5sam/ScanUS/cam_pos.jpg

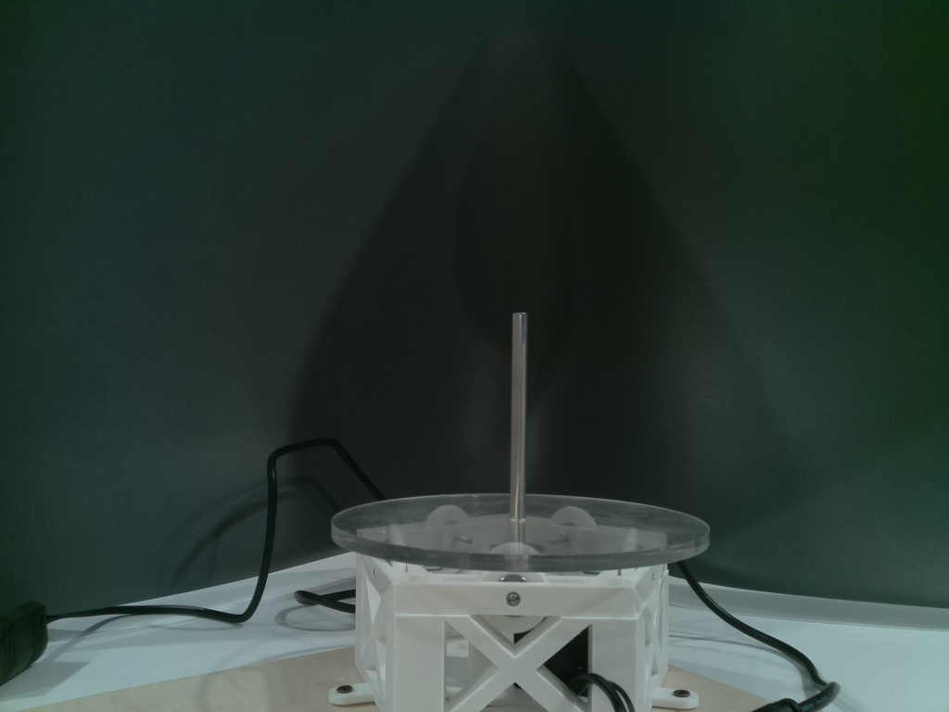
cam_pos.jpg
