5sam/ScanUS/Images/bon_laser_boite.jpg

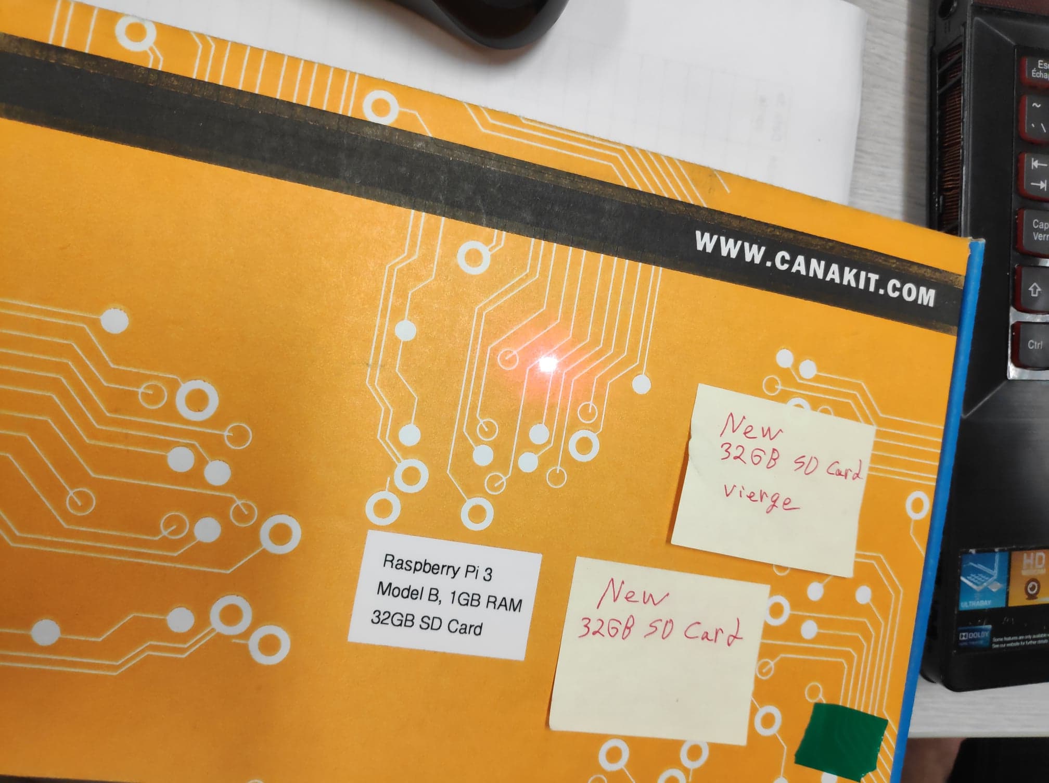
Images/bon_laser_boite.jpg
