5sam/ScanUS/Images/bon_laser_papier.jpg

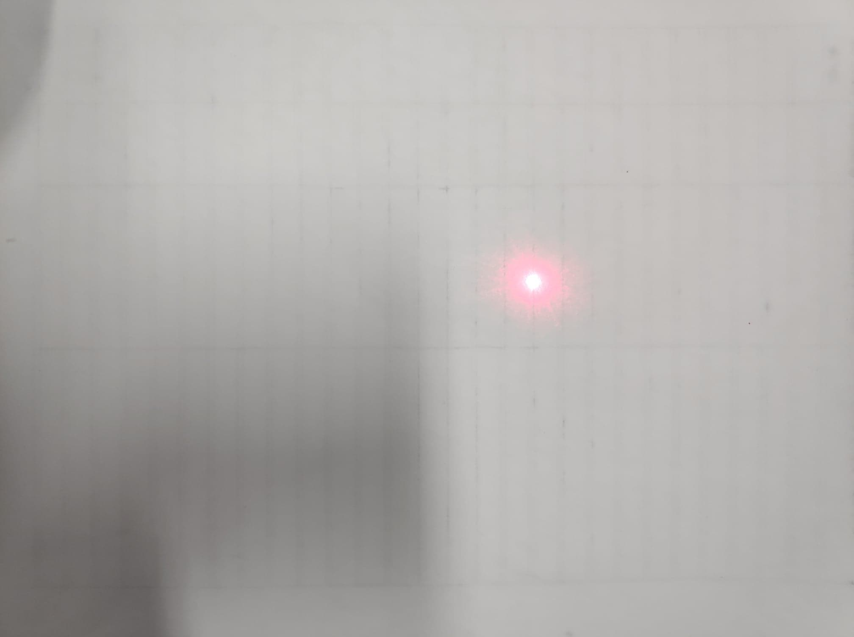
Images/bon_laser_papier.jpg
