5sam/ScanUS/Images/bon_laser_souris_1.jpg

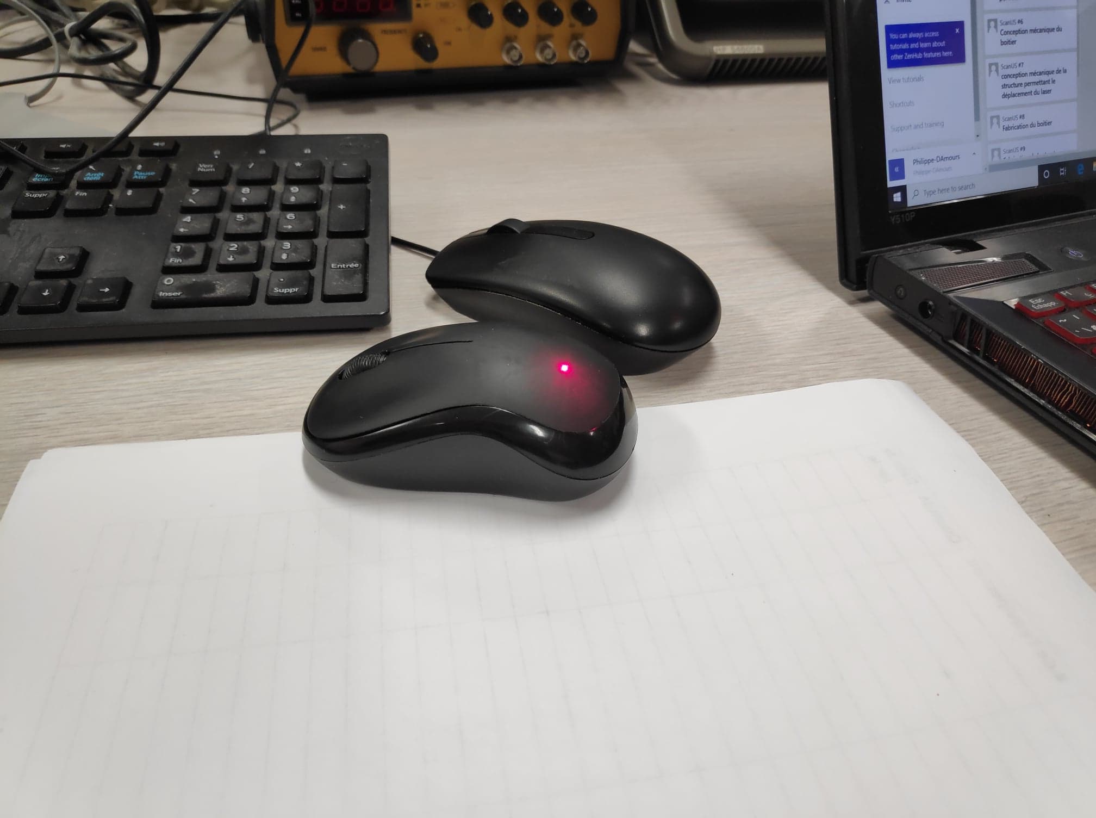
Images/bon_laser_souris_1.jpg
