5sam/ScanUS/Images/bon_laser_souris_2.jpg

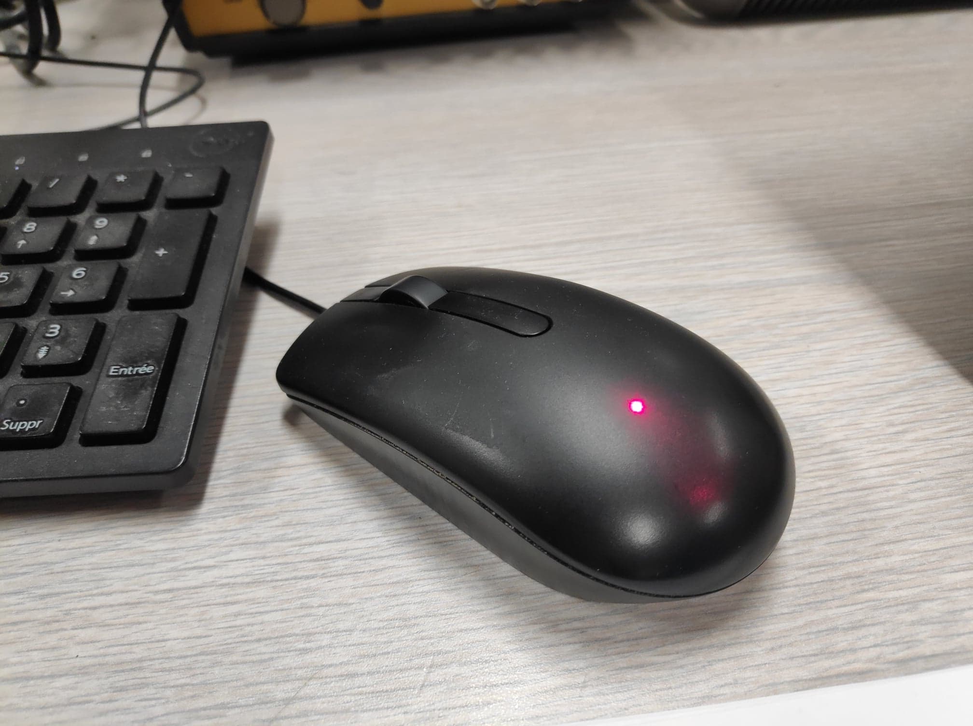
Images/bon_laser_souris_2.jpg
