5sam/ScanUS/Images/red_dot.jpg

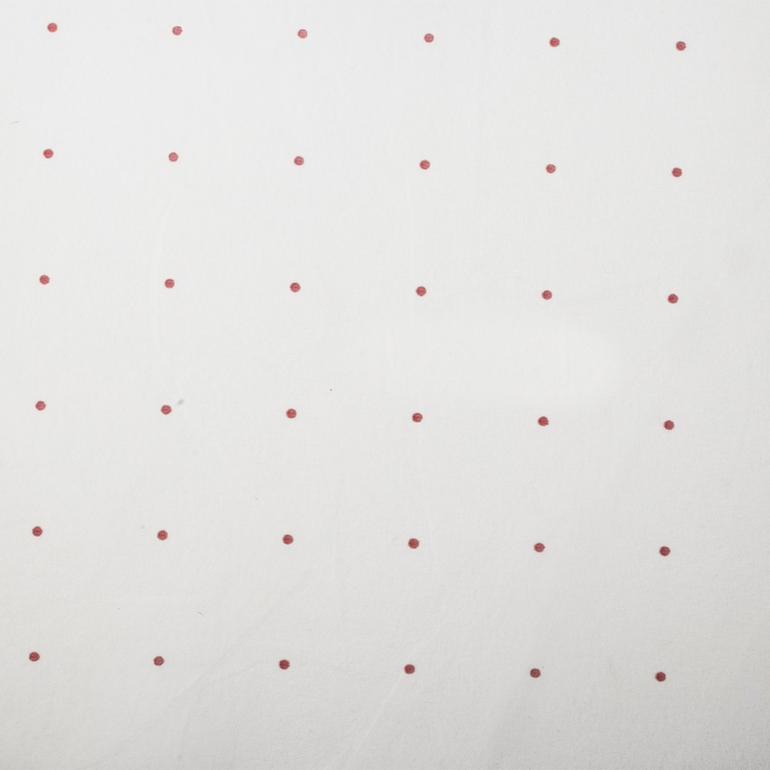
Images/red_dot.jpg
