5sam/ScanUS/imagetestjuan.jpg

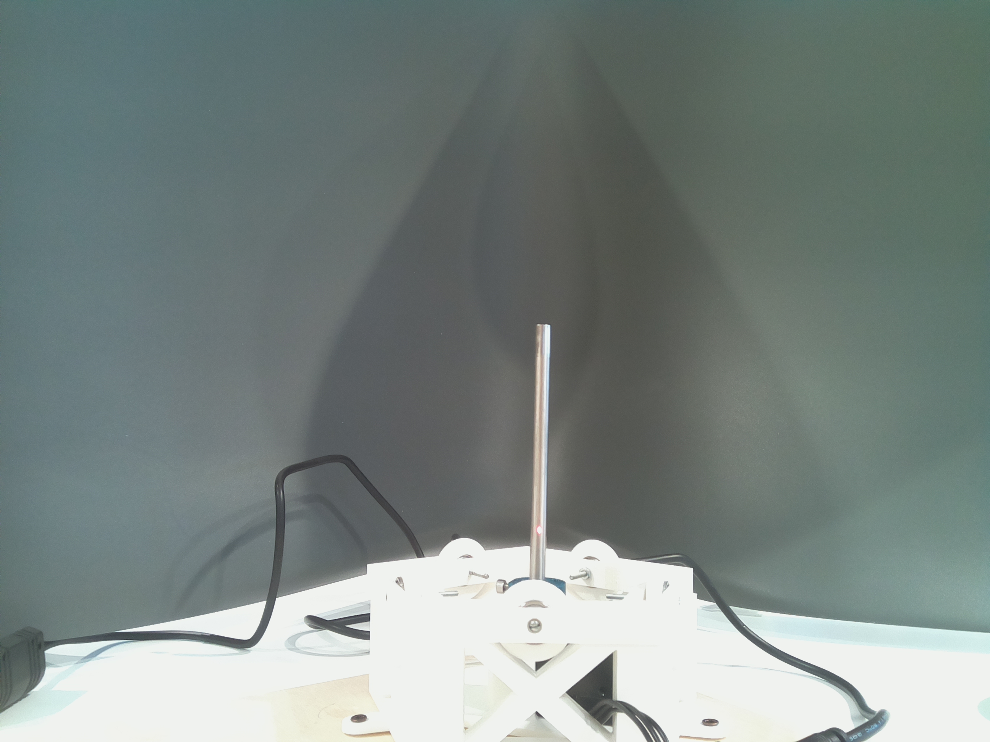
imagetestjuan.jpg
