5sam/ScanUS/Calibration/image_0.png

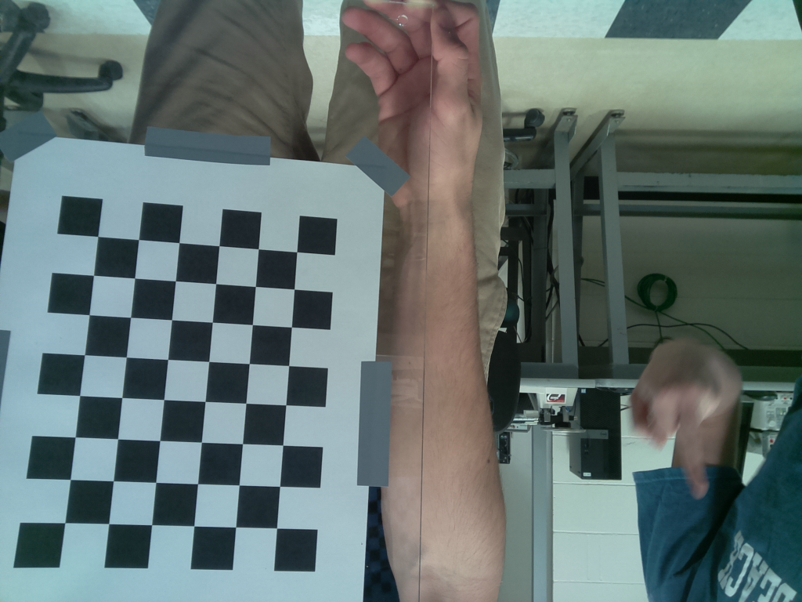
Calibration/image_0.png
