5sam/ScanUS/Calibration/image_1.png

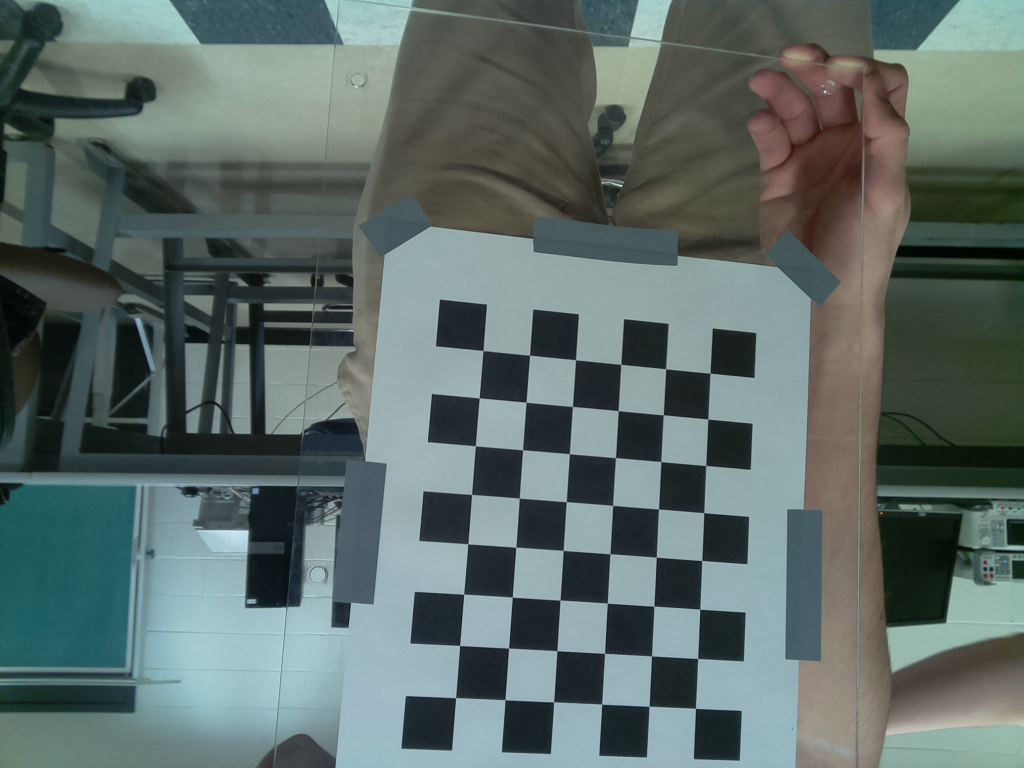
Calibration/image_1.png
