5sam/ScanUS/Calibration/image_2.png

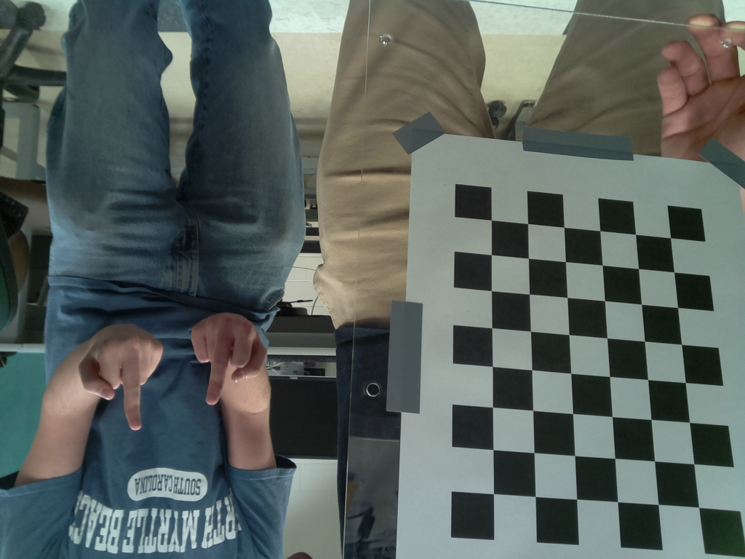
Calibration/image_2.png
