5sam/ScanUS/Calibration/image_3.png

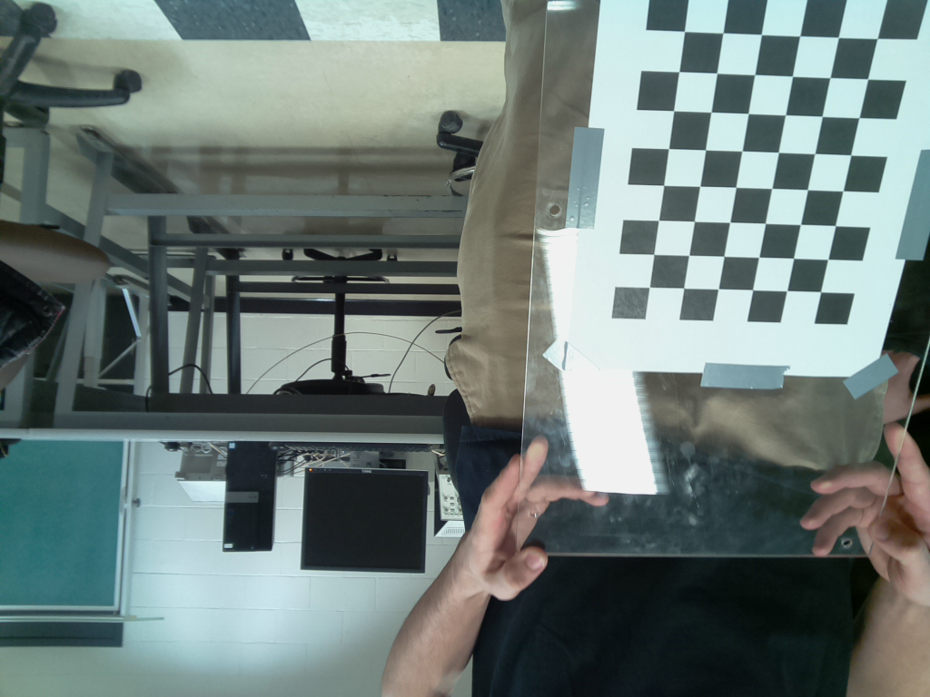
Calibration/image_3.png
