5sam/ScanUS/Calibration/image_4.png

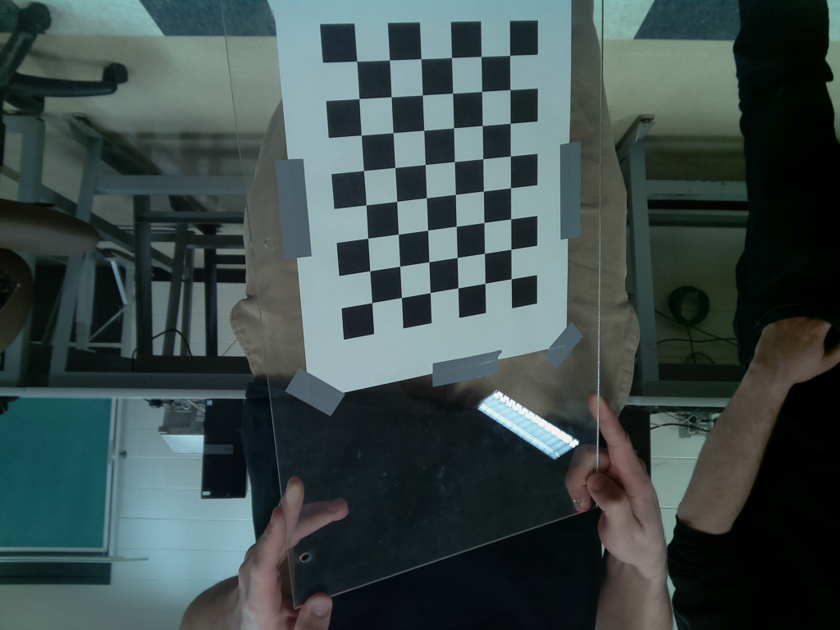
Calibration/image_4.png
