5sam/ScanUS/Calibration/image_5.png

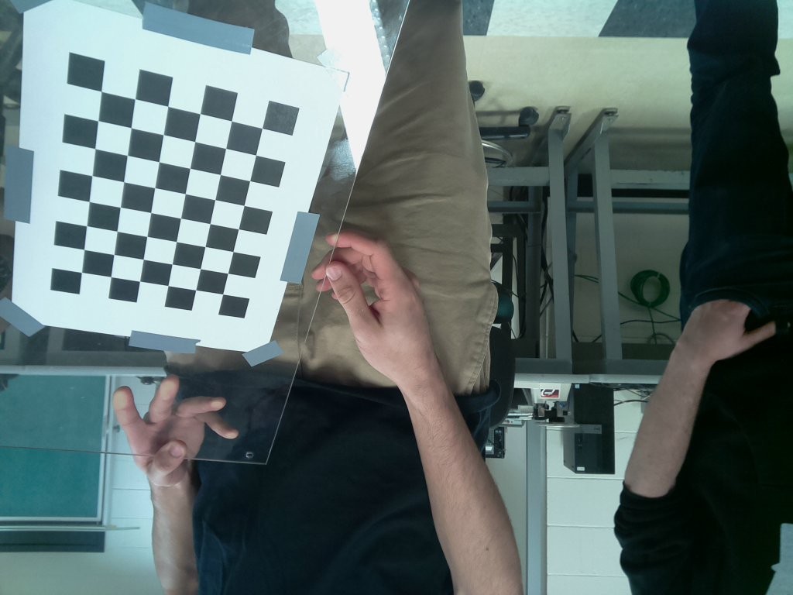
Calibration/image_5.png
