5sam/ScanUS/Calibration/image_6.png

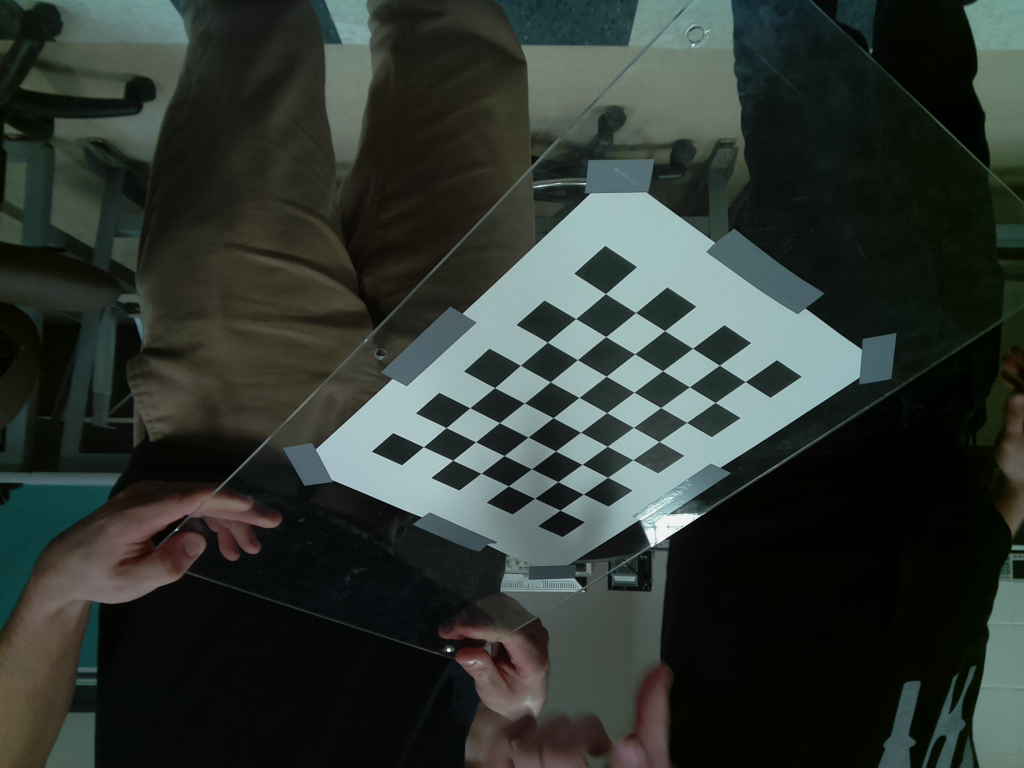
Calibration/image_6.png
