5sam/ScanUS/Calibration/image_7.png

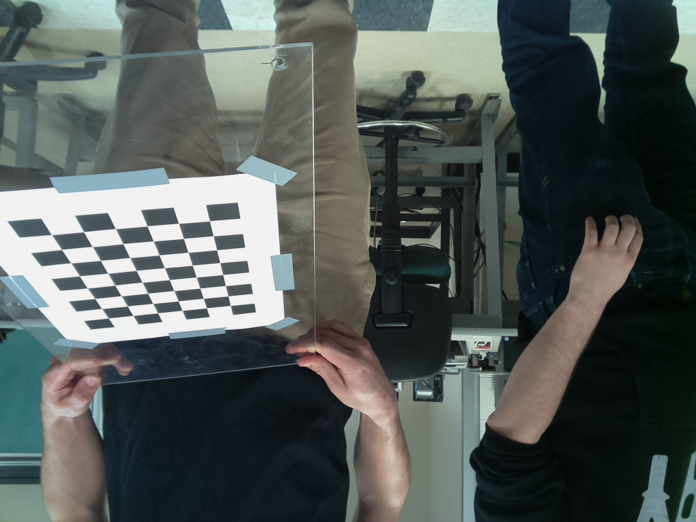
Calibration/image_7.png
