5sam/ScanUS/Calibration/image_8.png

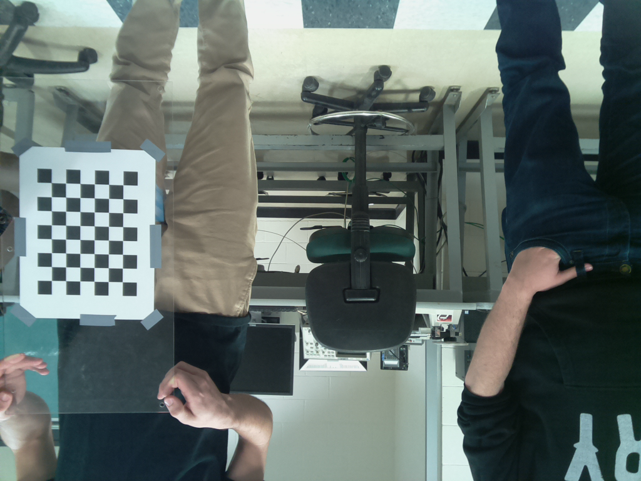
Calibration/image_8.png
