5sam/ScanUS/Calibration/image_9.png

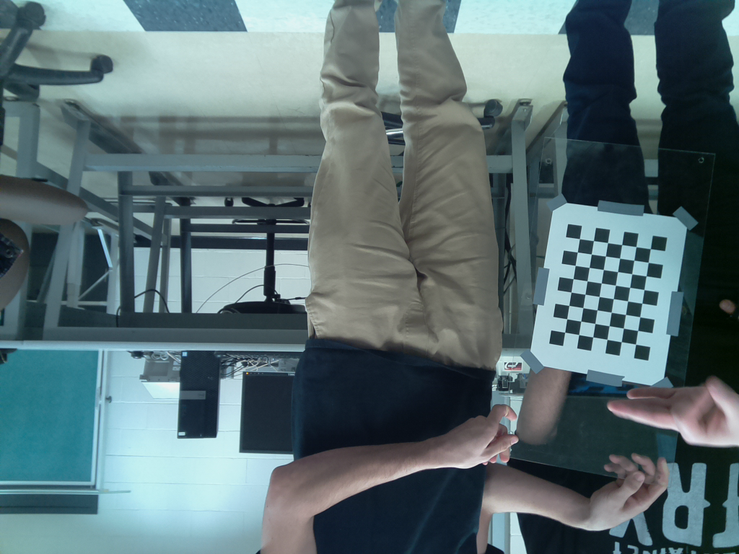
Calibration/image_9.png
