5sam/ScanUS/Calibration/image_11.png

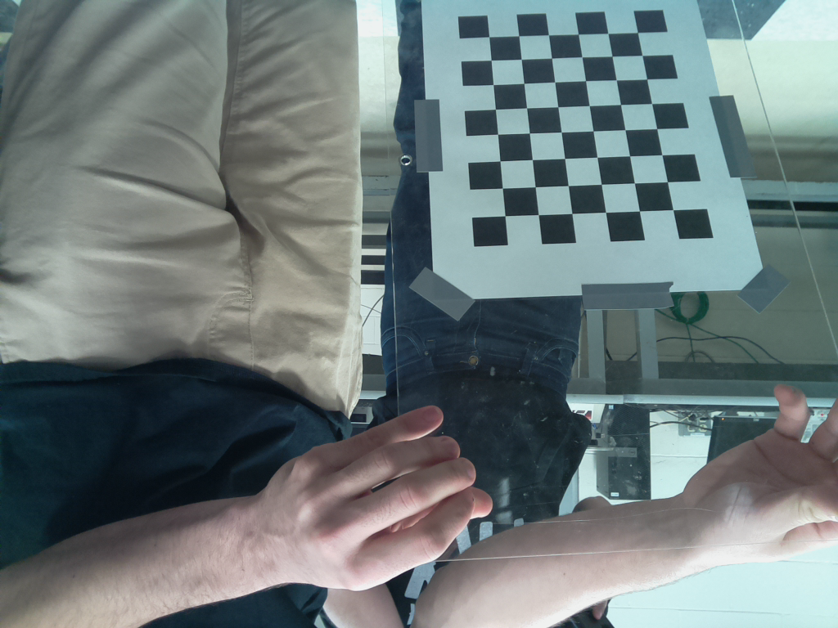
Calibration/image_11.png
