5sam/ScanUS/Calibration/image_12.png

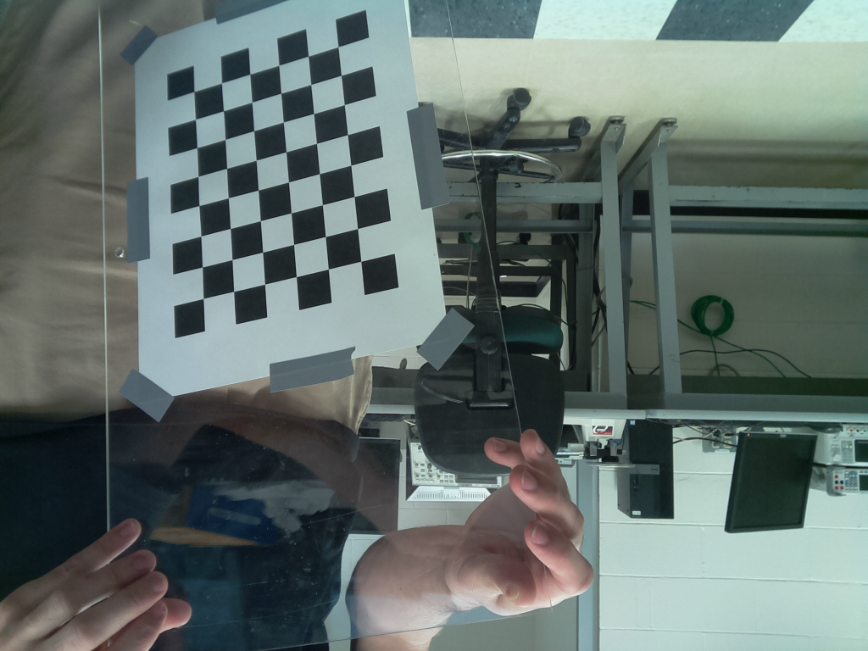
Calibration/image_12.png
