5sam/ScanUS/Calibration/image_13.png

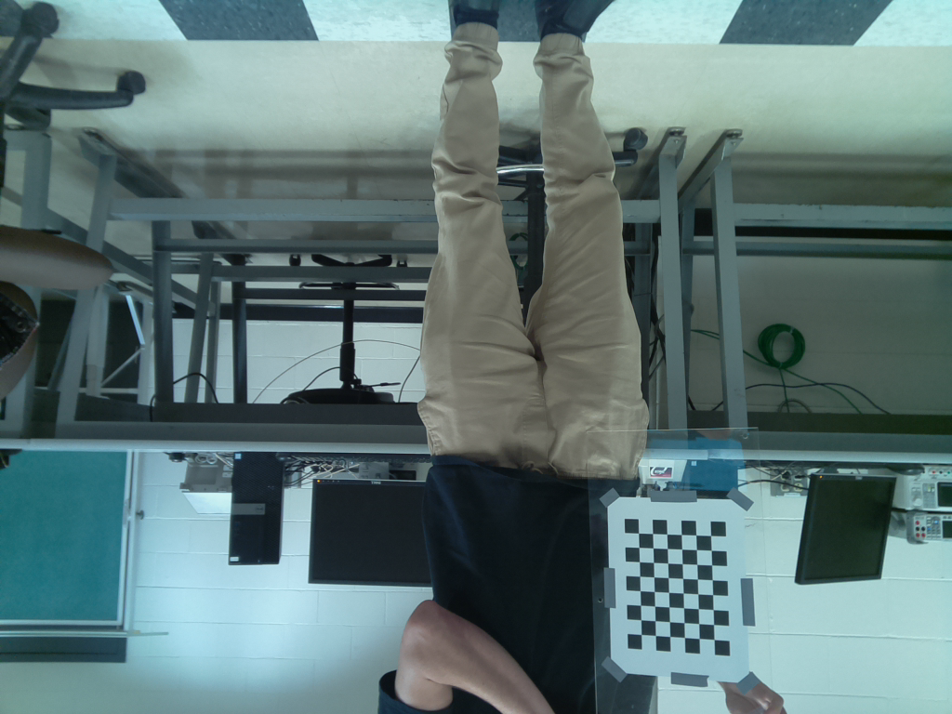
Calibration/image_13.png
