5sam/ScanUS/Calibration/image_14.png

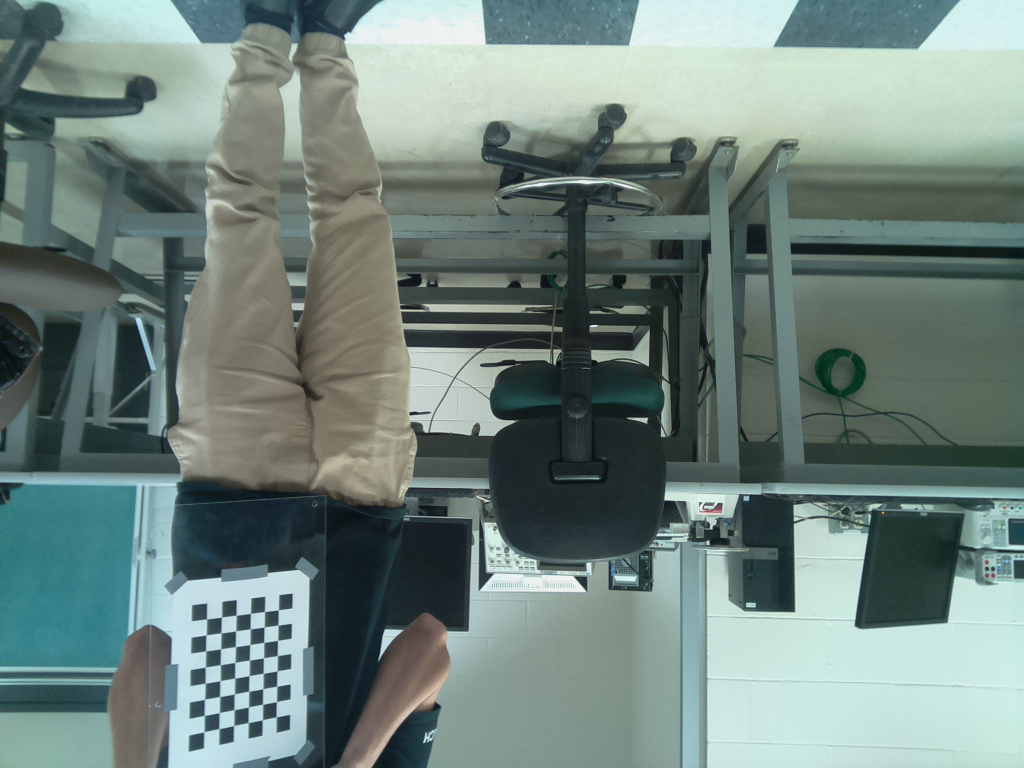
Calibration/image_14.png
