5sam/ScanUS/Calibration/image_15.png

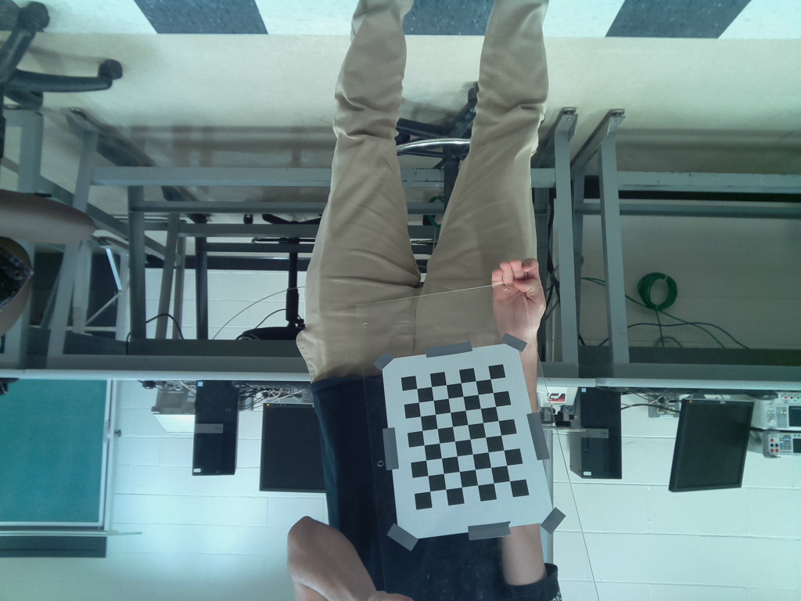
Calibration/image_15.png
