5sam/ScanUS/Calibration/image_16.png

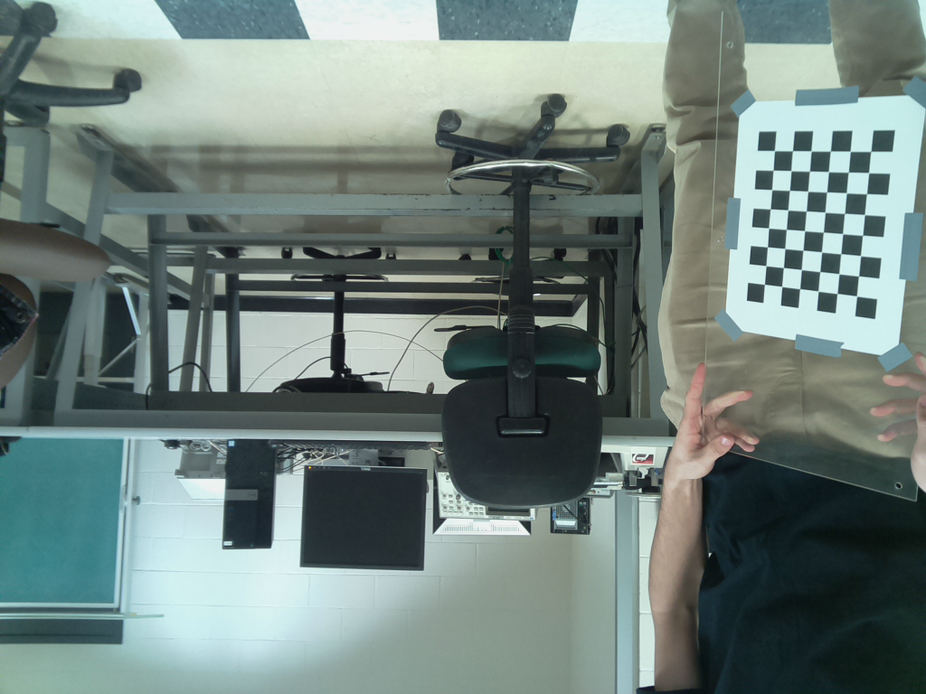
Calibration/image_16.png
