5sam/ScanUS/Calibration/image_17.png

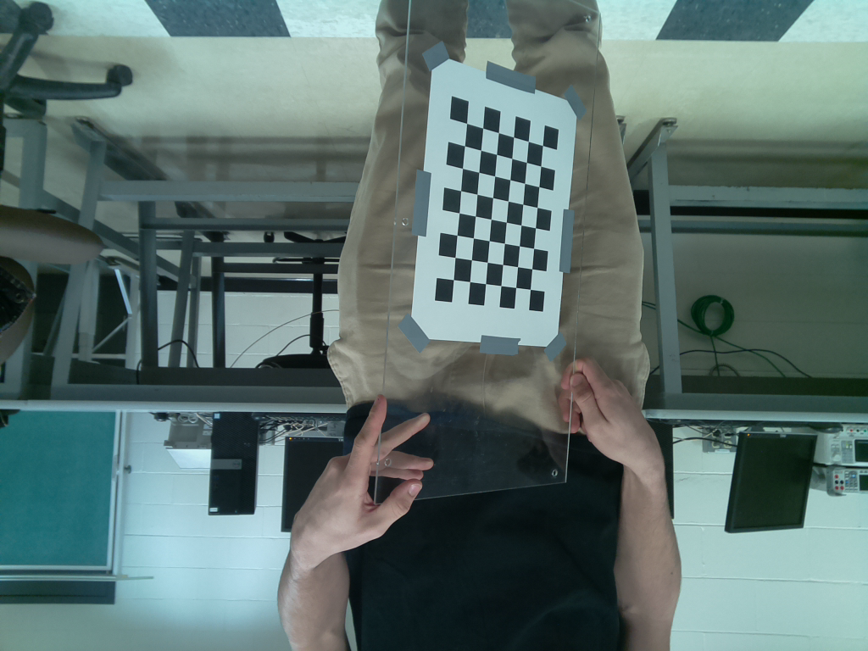
Calibration/image_17.png
