5sam/ScanUS/Calibration/image_19.png

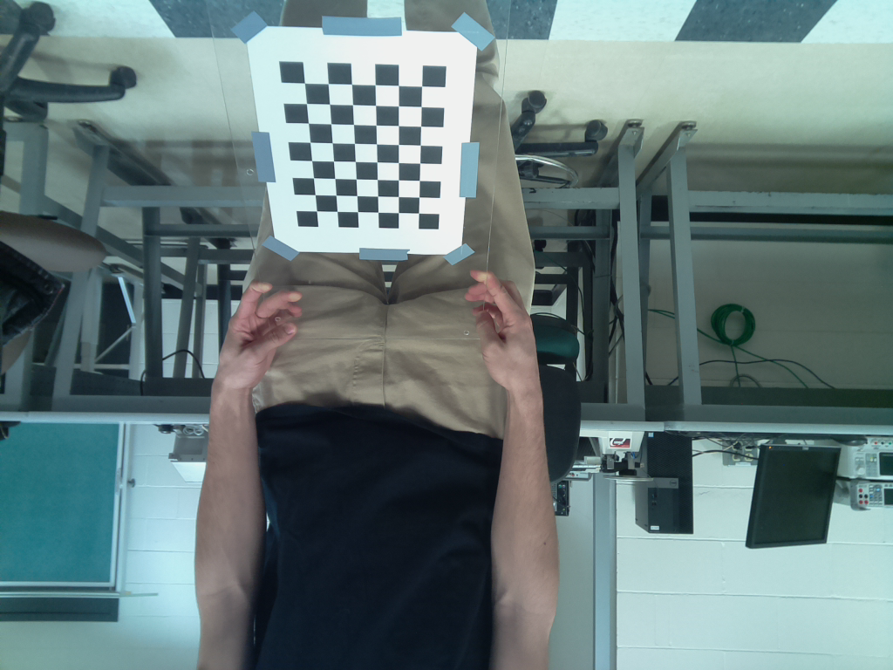
Calibration/image_19.png
