5sam/ScanUS/Calibration/image_20.png

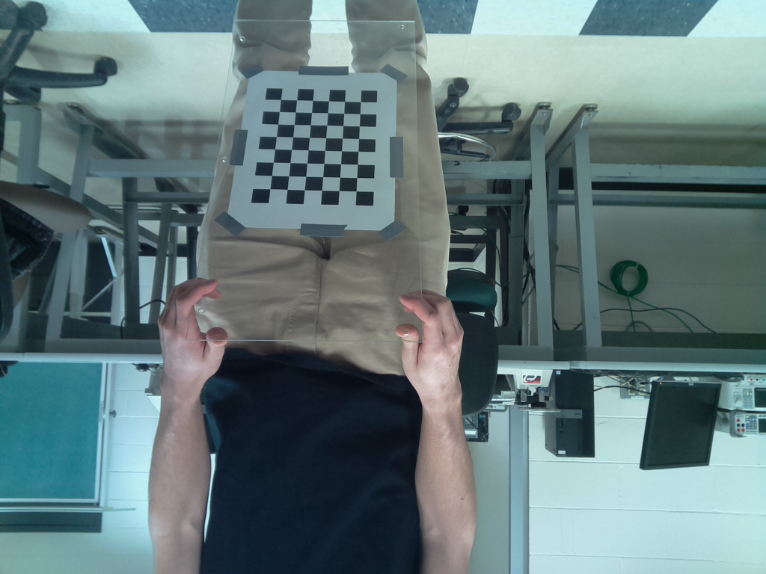
Calibration/image_20.png
