5sam/ScanUS/Calibration/image_21.png

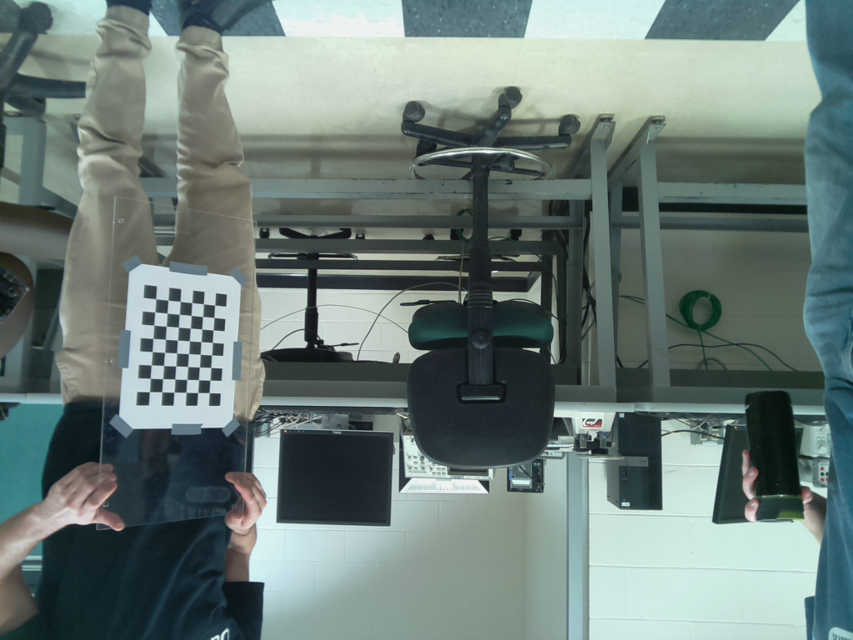
Calibration/image_21.png
