5sam/ScanUS/Calibration/image_23.png

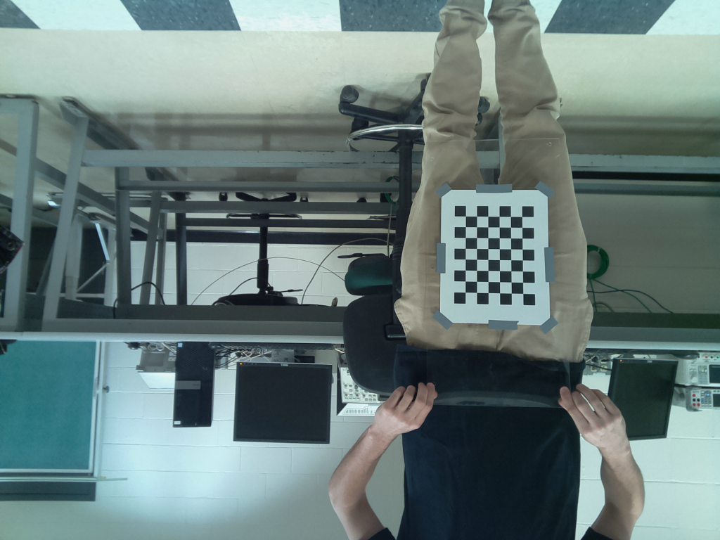
Calibration/image_23.png
