5sam/ScanUS/Calibration/image_24.png

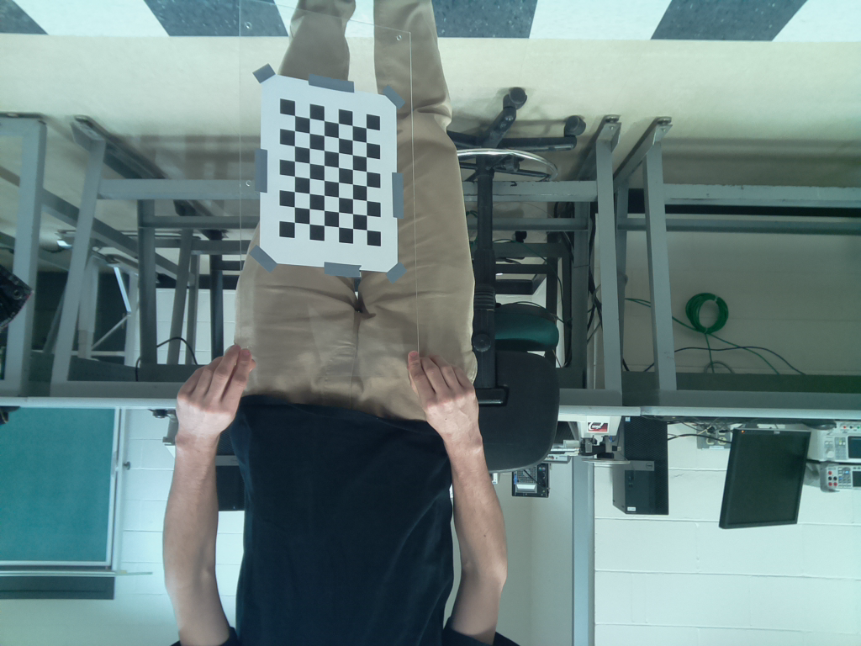
Calibration/image_24.png
