5sam/ScanUS/Calibration/image_25.png

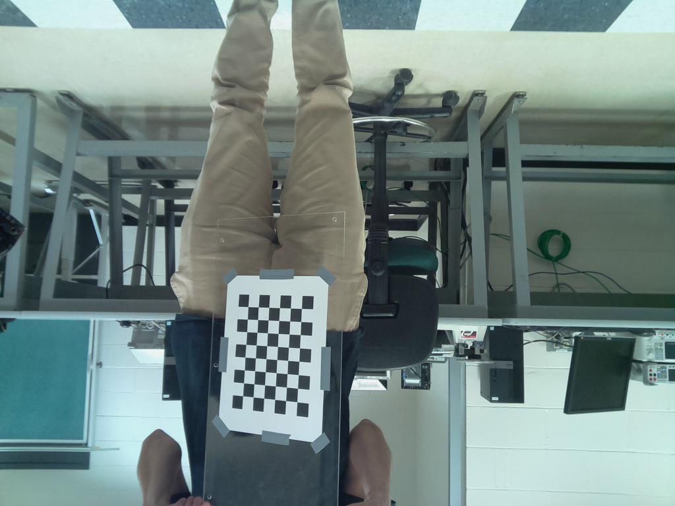
Calibration/image_25.png
