5sam/ScanUS/Calibration/image_26.png

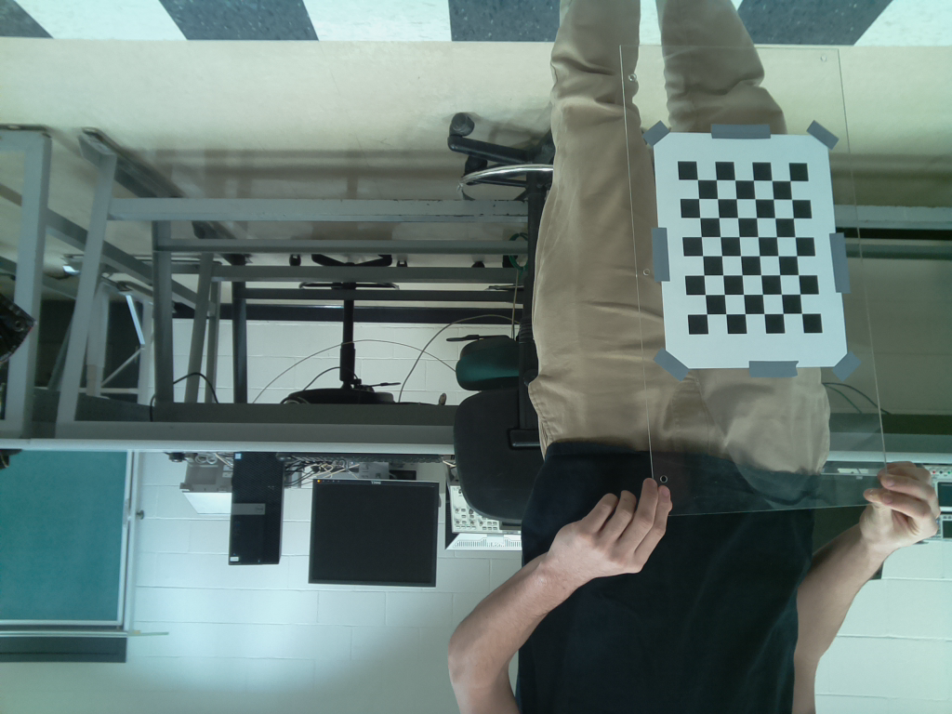
Calibration/image_26.png
