5sam/ScanUS/Calibration/image_27.png

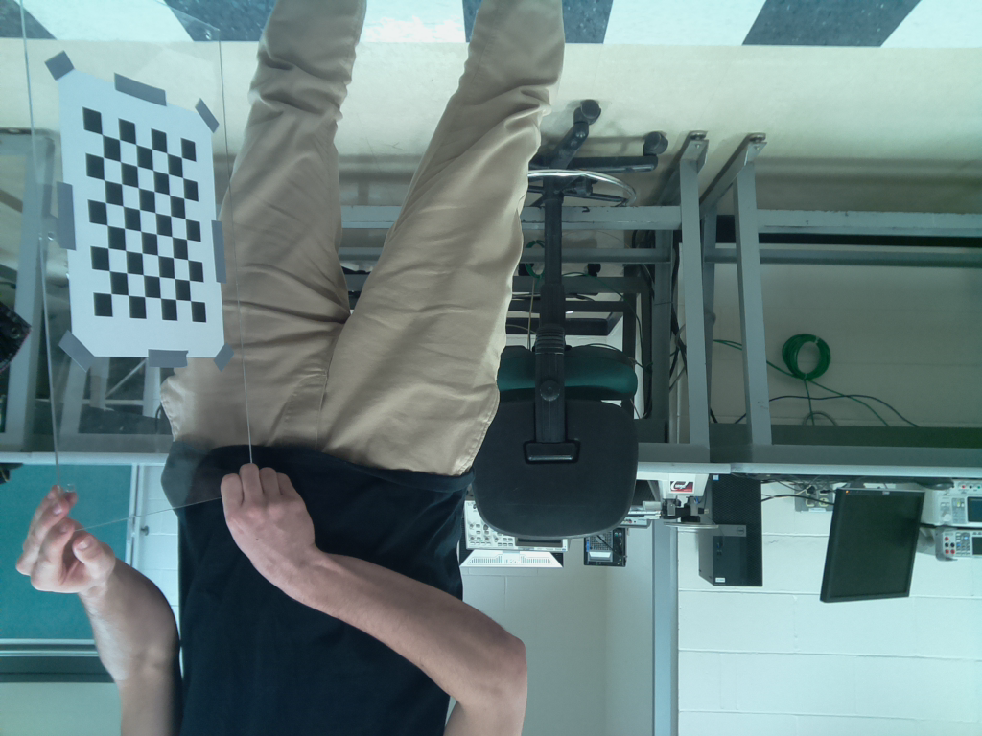
Calibration/image_27.png
