5sam/ScanUS/Calibration/image_28.png

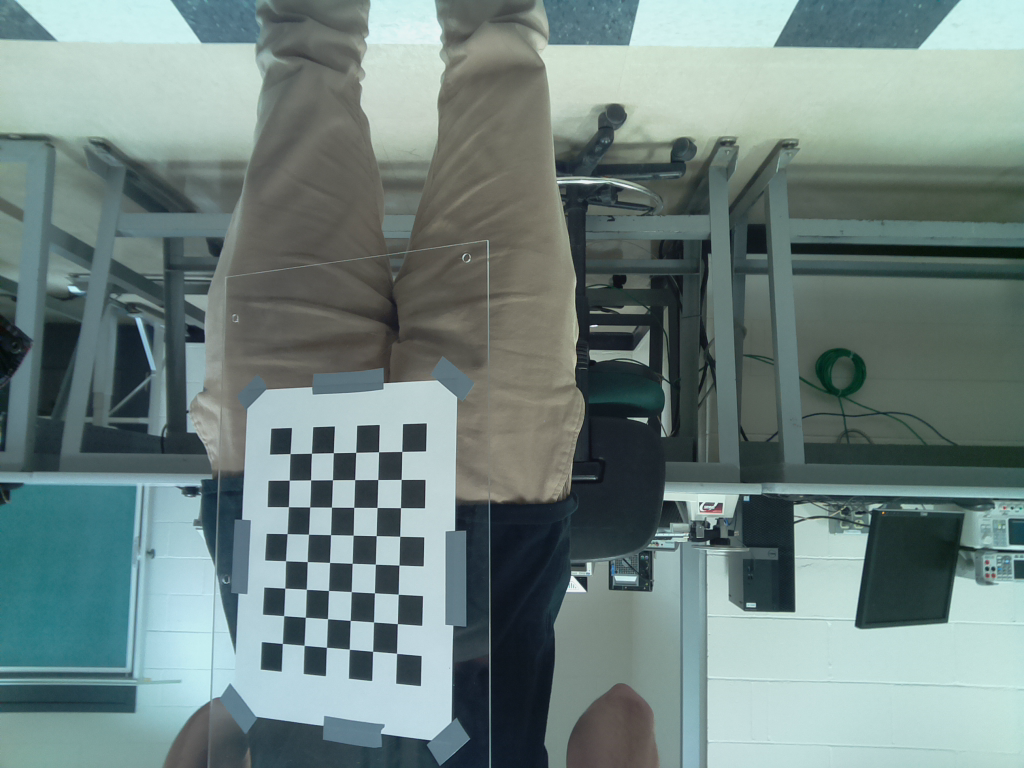
Calibration/image_28.png
