5sam/ScanUS/Calibration/image_29.png

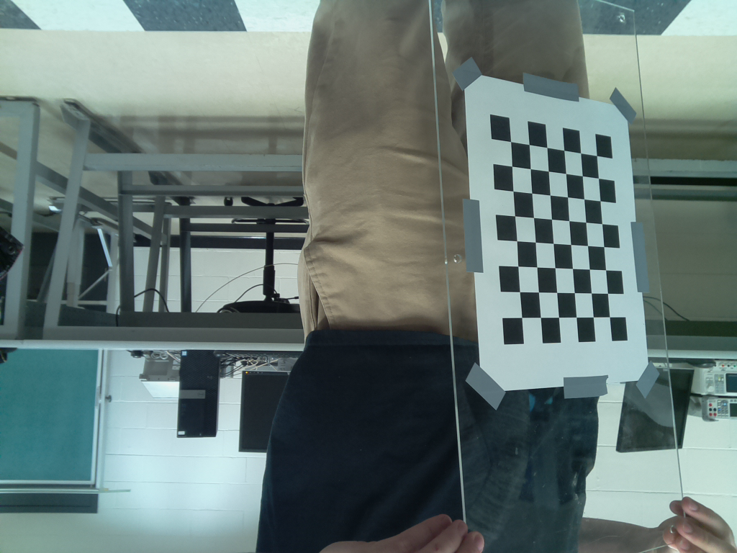
Calibration/image_29.png
