5sam/ScanUS/Calibration/image_30.png

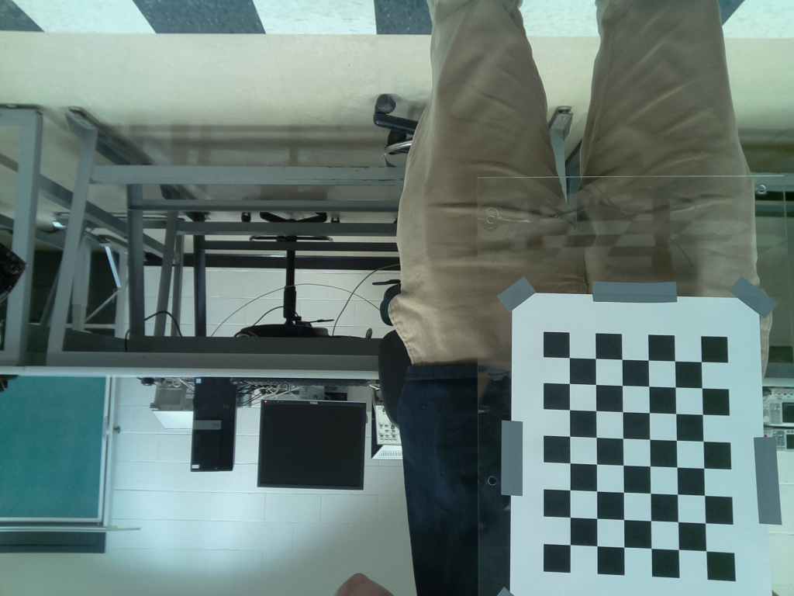
Calibration/image_30.png
