5sam/ScanUS/Calibration/image_31.png

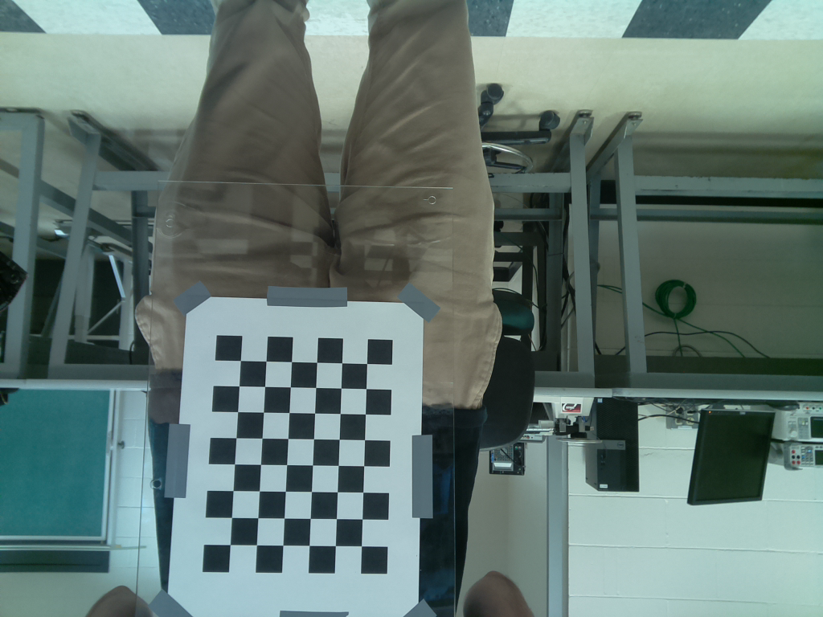
Calibration/image_31.png
