5sam/ScanUS/Calibration/image_32.png

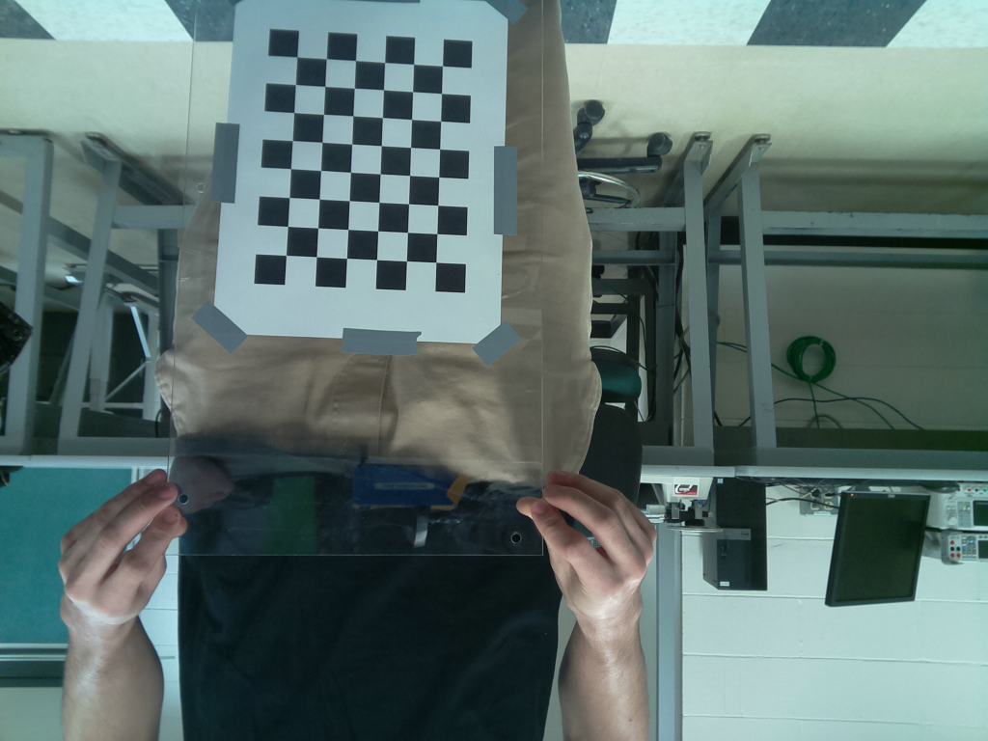
Calibration/image_32.png
