5sam/ScanUS/Calibration/image_33.png

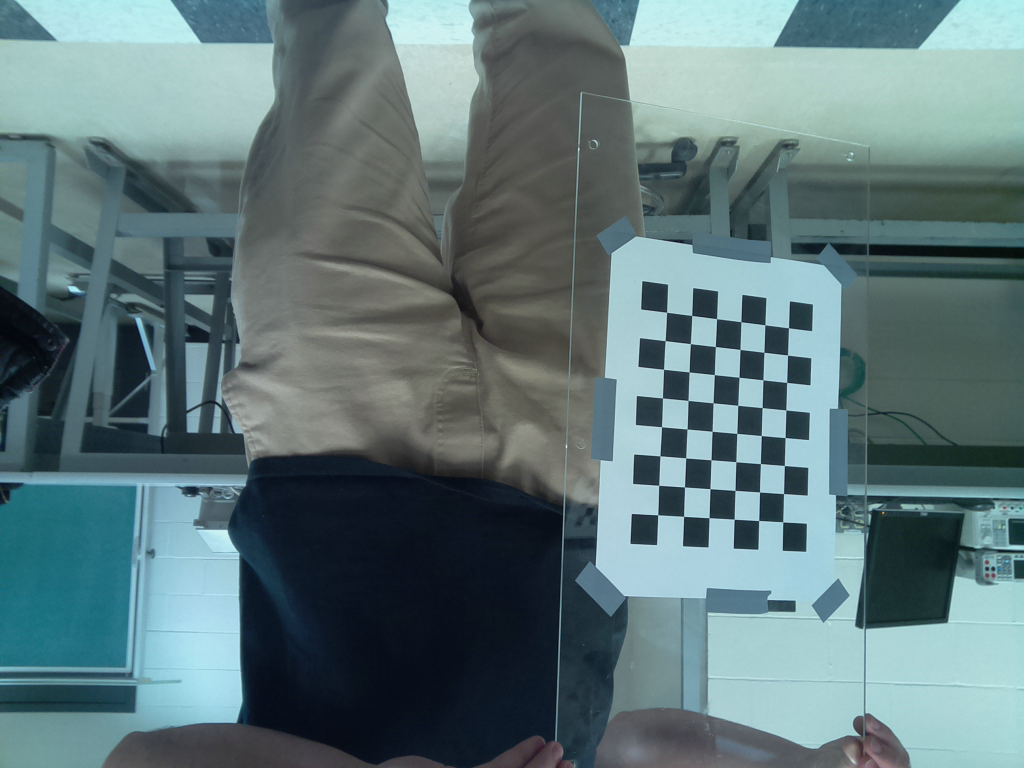
Calibration/image_33.png
