5sam/ScanUS/Calibration/image_34.png

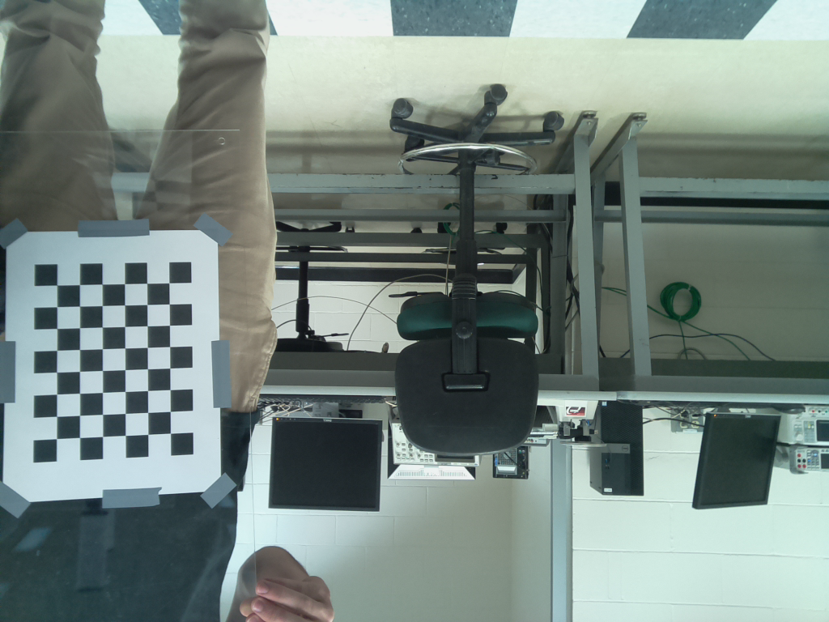
Calibration/image_34.png
