5sam/ScanUS/Calibration/image_35.png

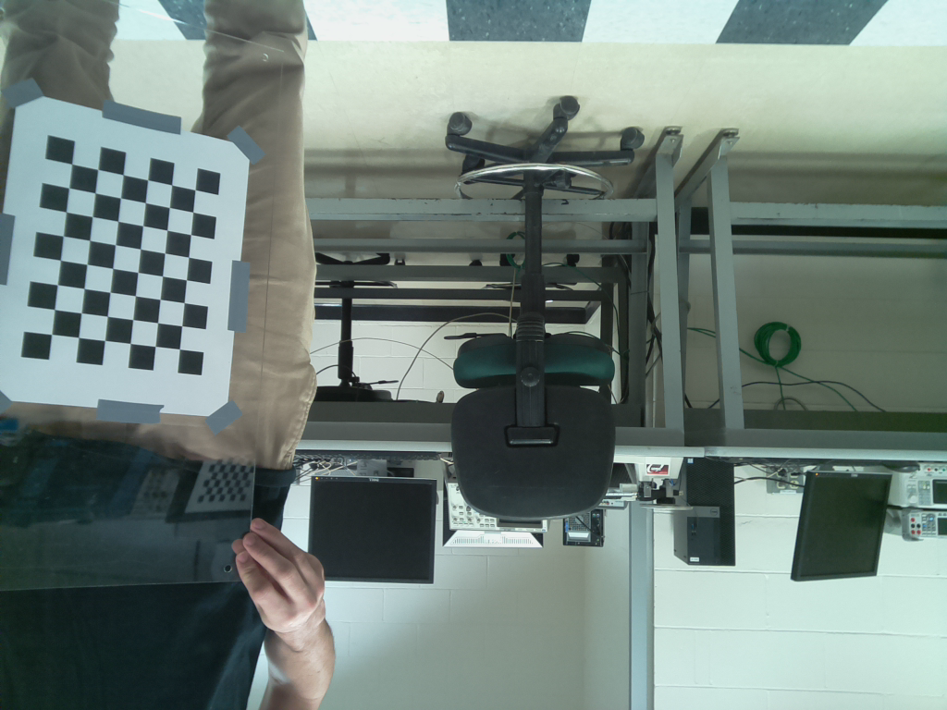
Calibration/image_35.png
