5sam/ScanUS/Calibration/image_36.png

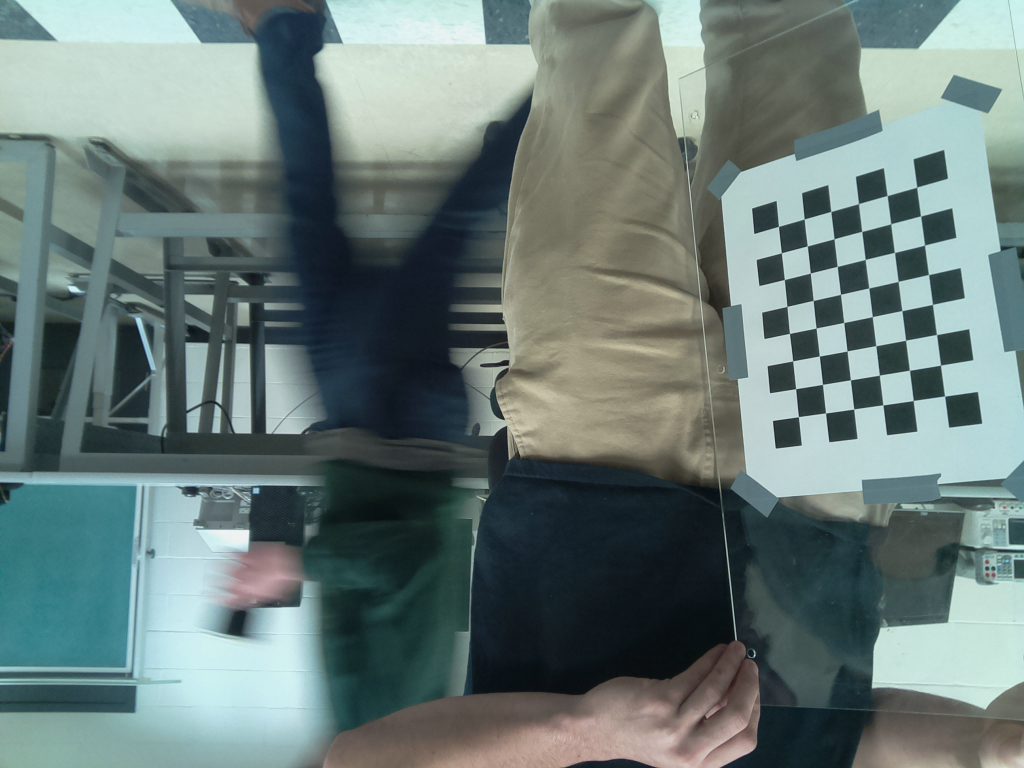
Calibration/image_36.png
