5sam/ScanUS/Calibration/image_39.png

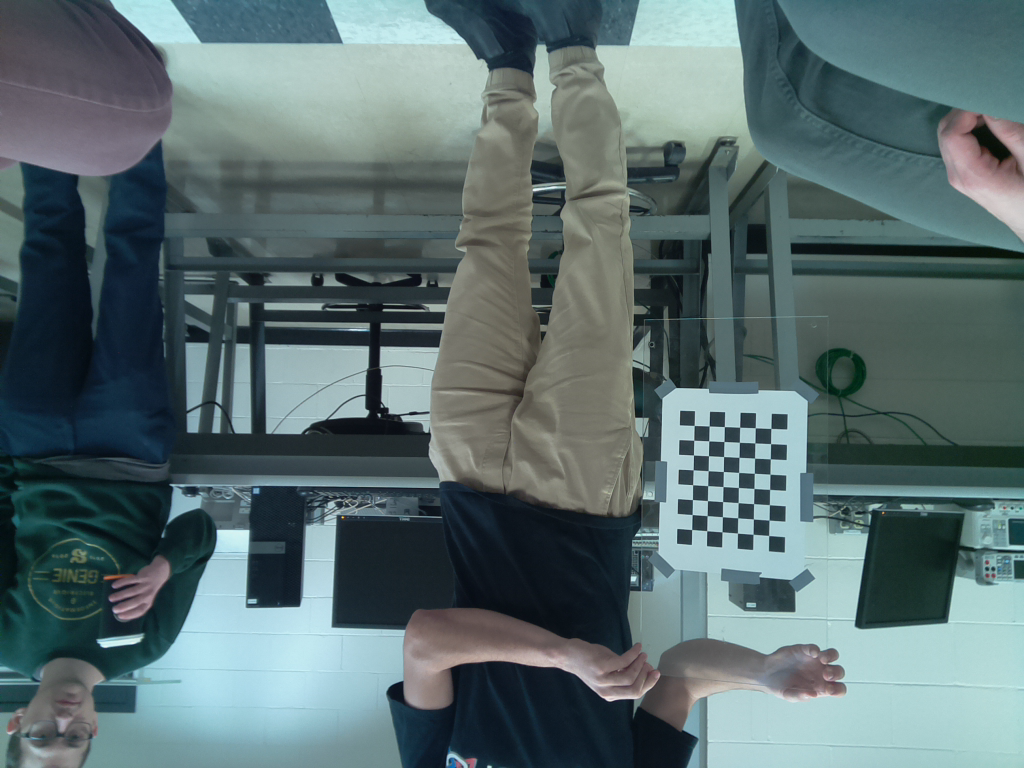
Calibration/image_39.png
