5sam/ScanUS/Calibration/image_40.png

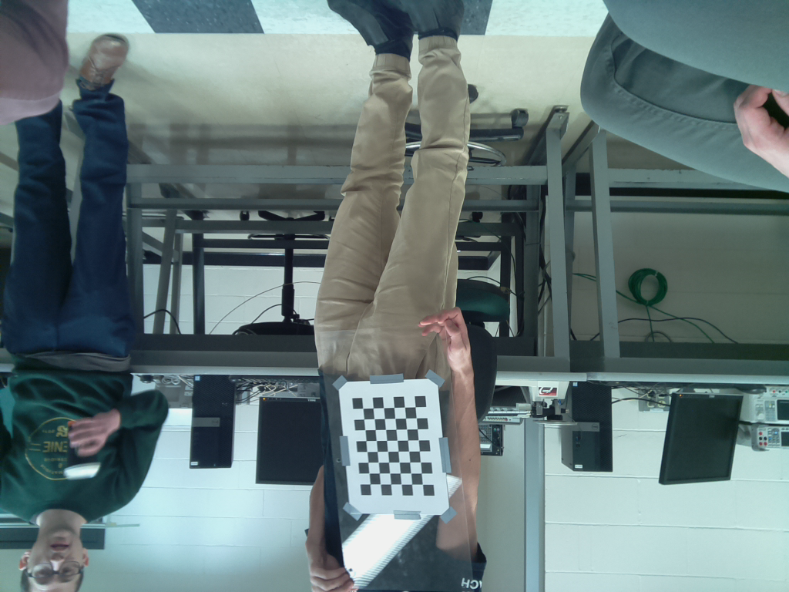
Calibration/image_40.png
