5sam/ScanUS/Calibration/image_41.png

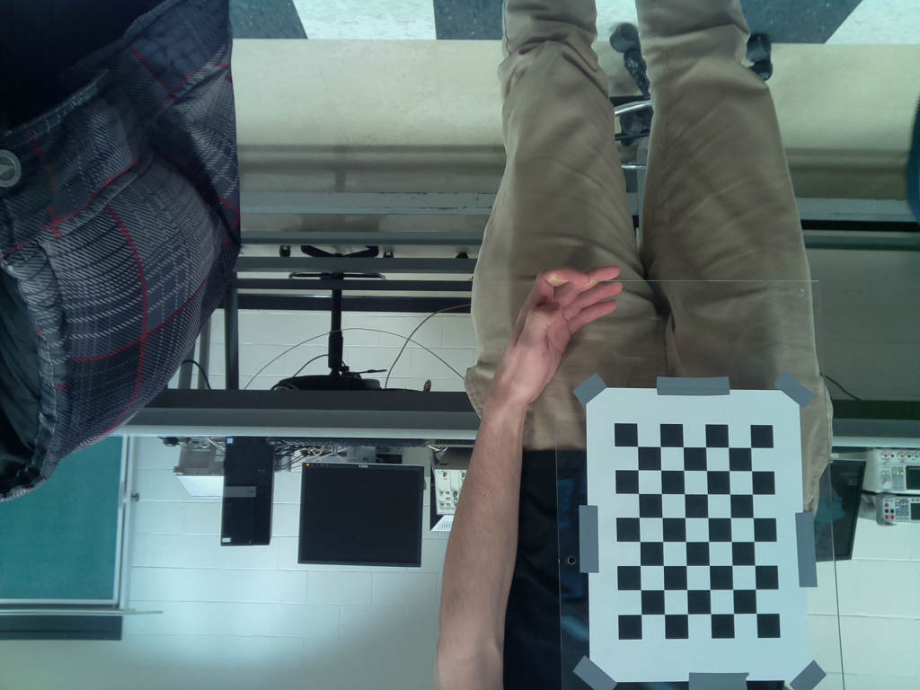
Calibration/image_41.png
