5sam/ScanUS/Calibration/image_42.png

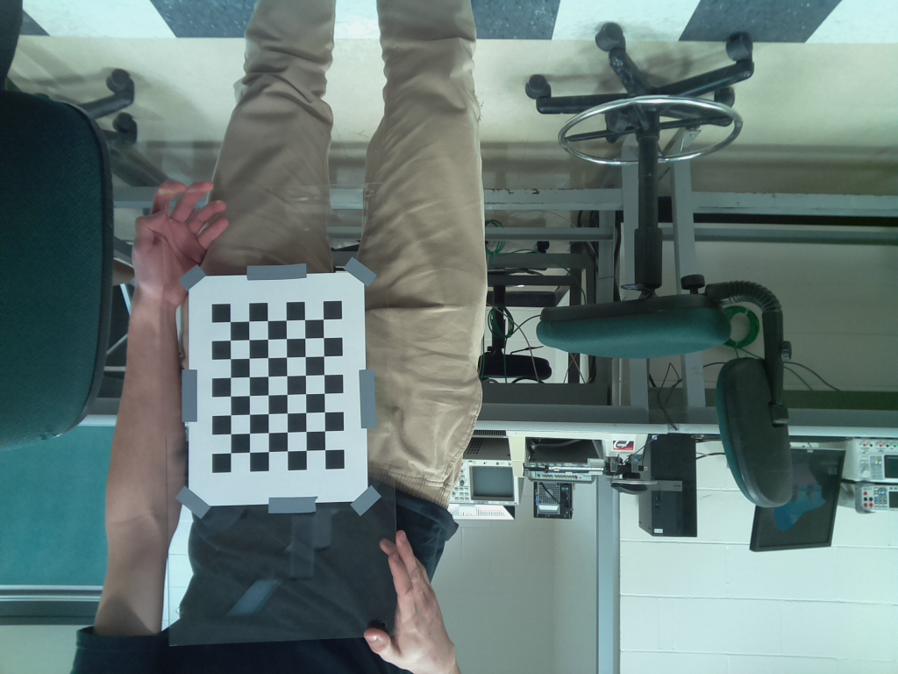
Calibration/image_42.png
