5sam/ScanUS/Calibration/image_43.png

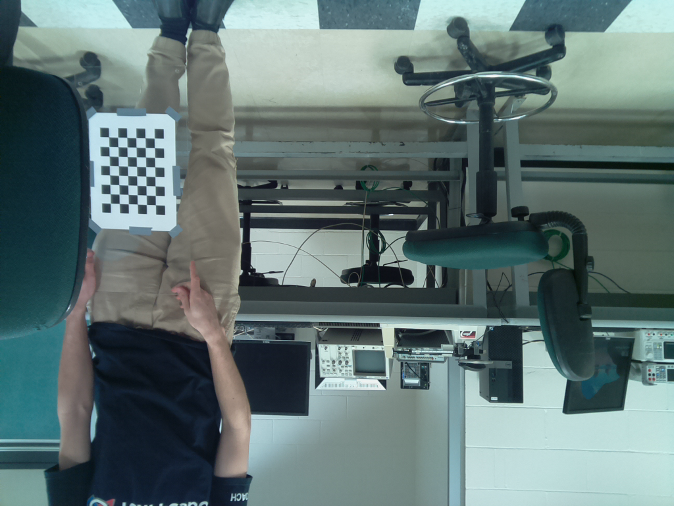
Calibration/image_43.png
