5sam/ScanUS/Calibration/image_44.png

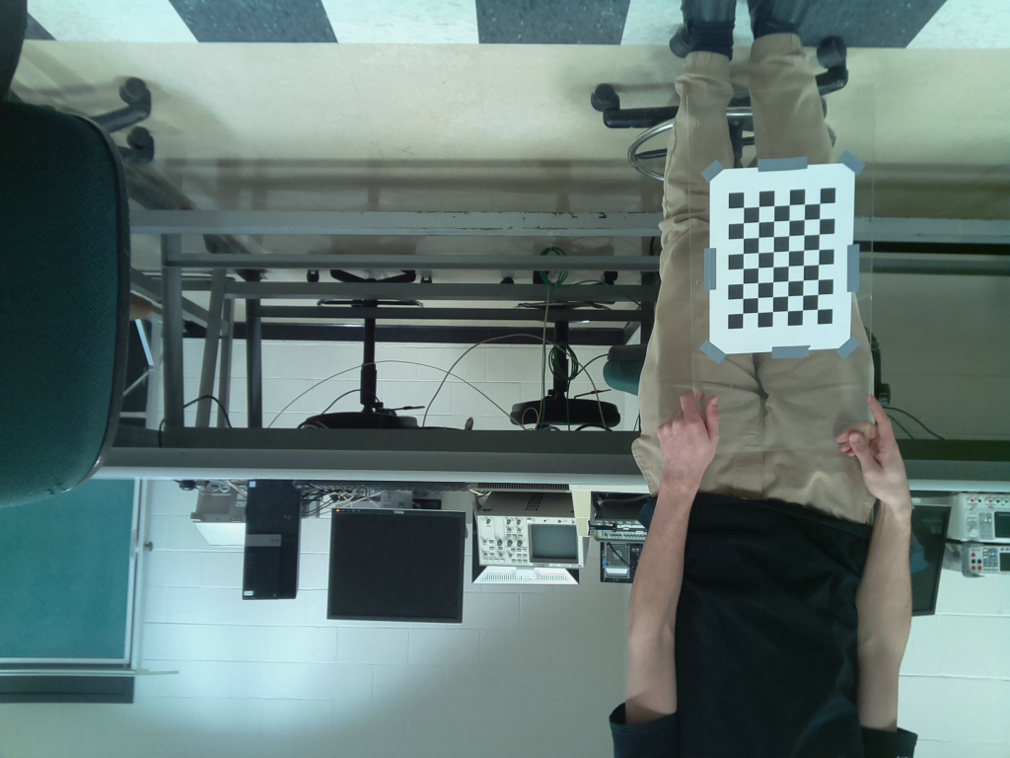
Calibration/image_44.png
