5sam/ScanUS/Calibration/image_45.png

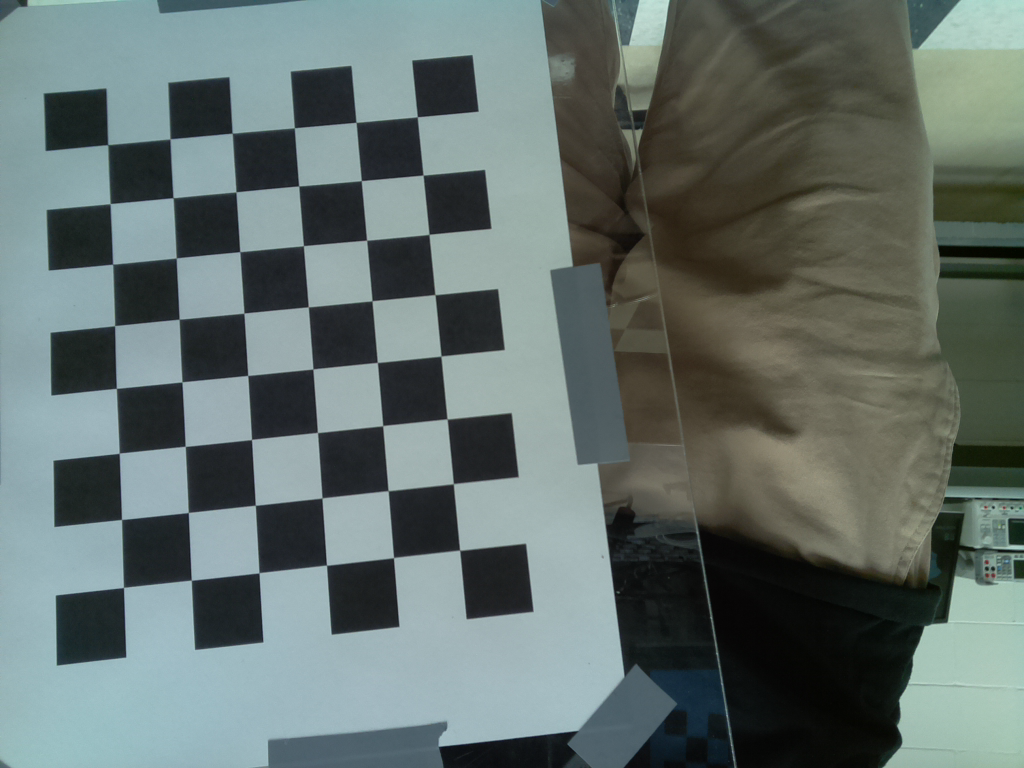
Calibration/image_45.png
