5sam/ScanUS/Calibration/image_46.png

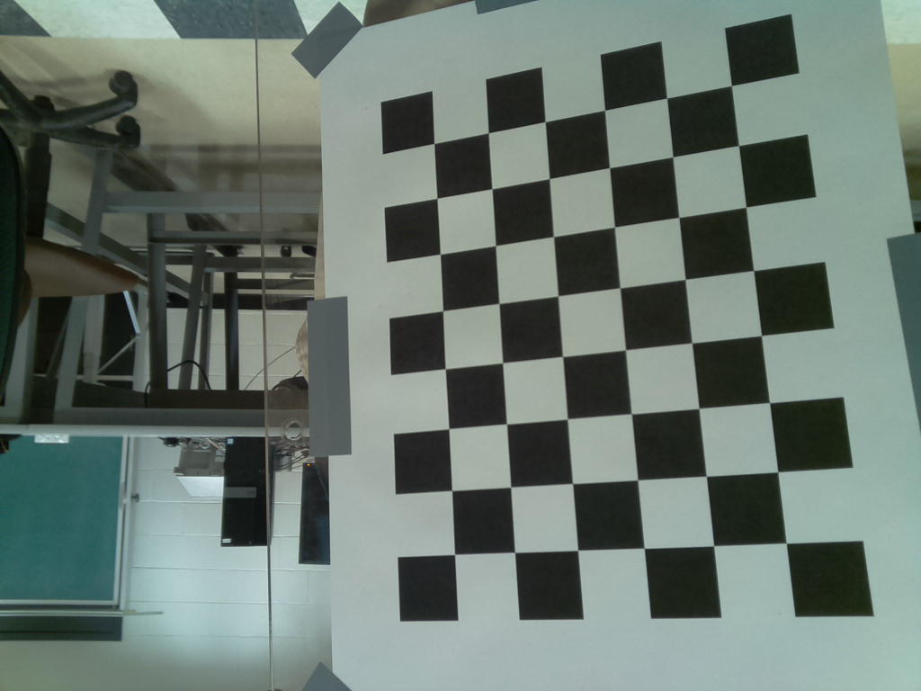
Calibration/image_46.png
