5sam/ScanUS/Calibration/image_47.png

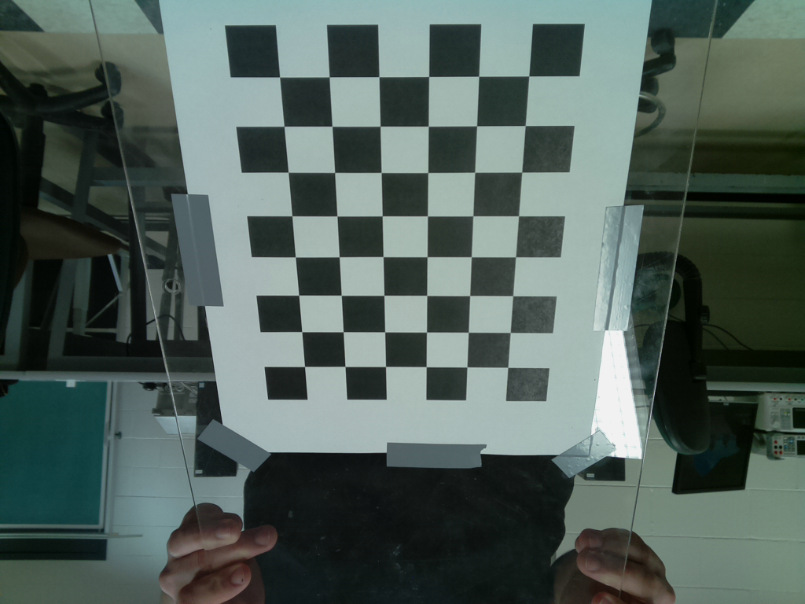
Calibration/image_47.png
