5sam/ScanUS/Calibration/image_48.png

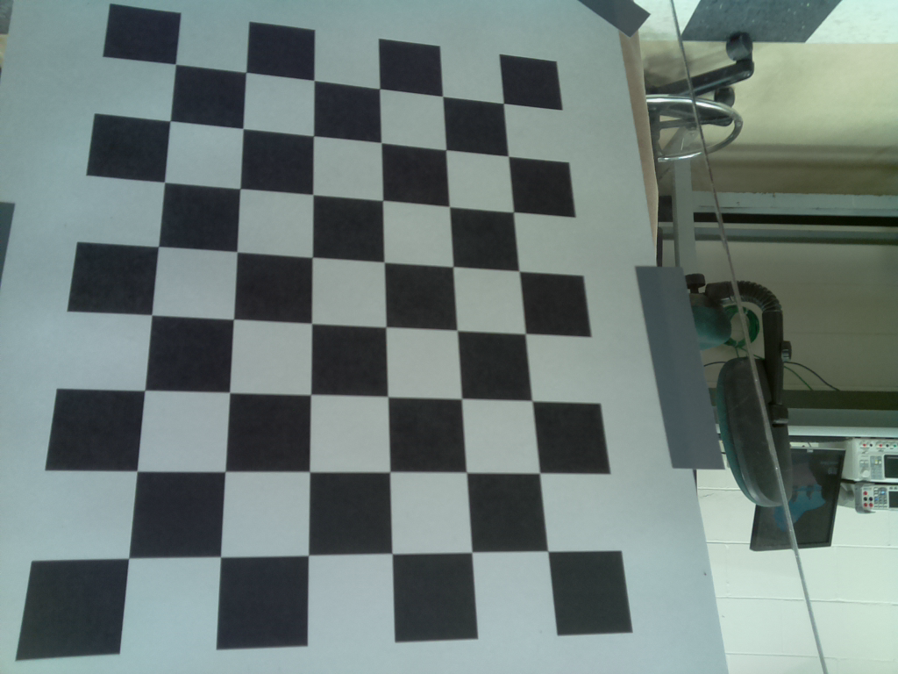
Calibration/image_48.png
