5sam/ScanUS/Calibration/image_49.png

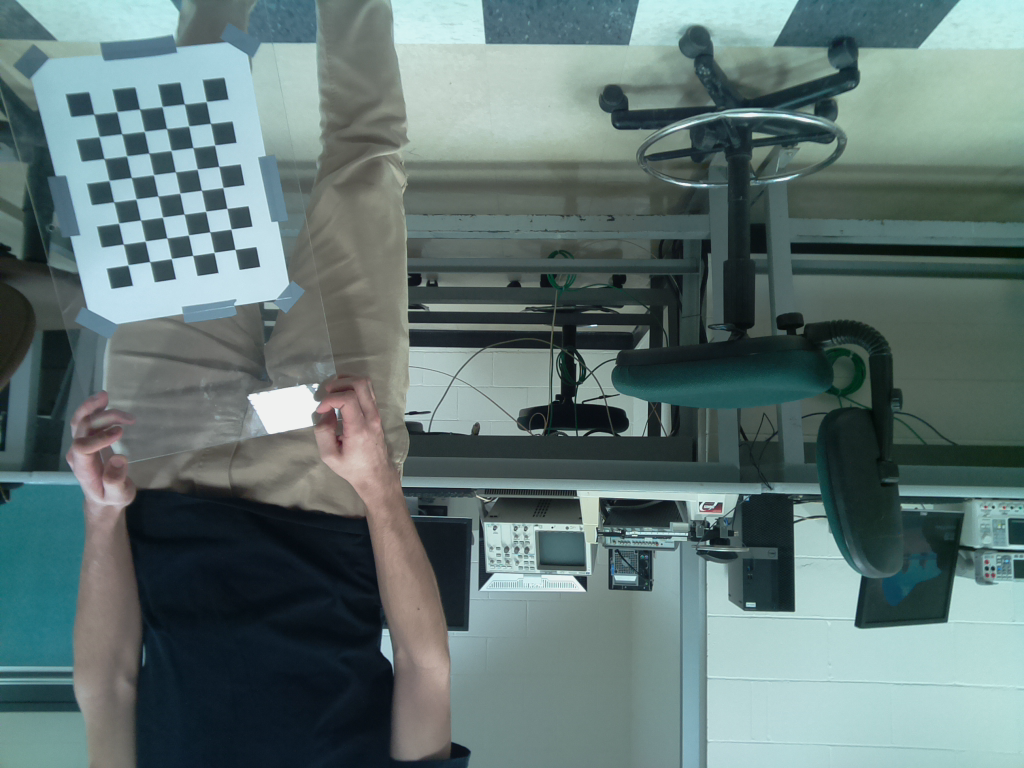
Calibration/image_49.png
