5sam/ScanUS/Calibration/image_50.png

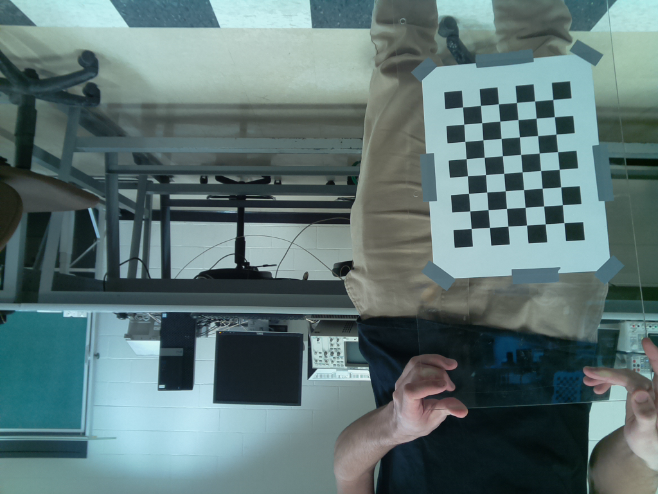
Calibration/image_50.png
