5sam/ScanUS/Calibration/image_51.png

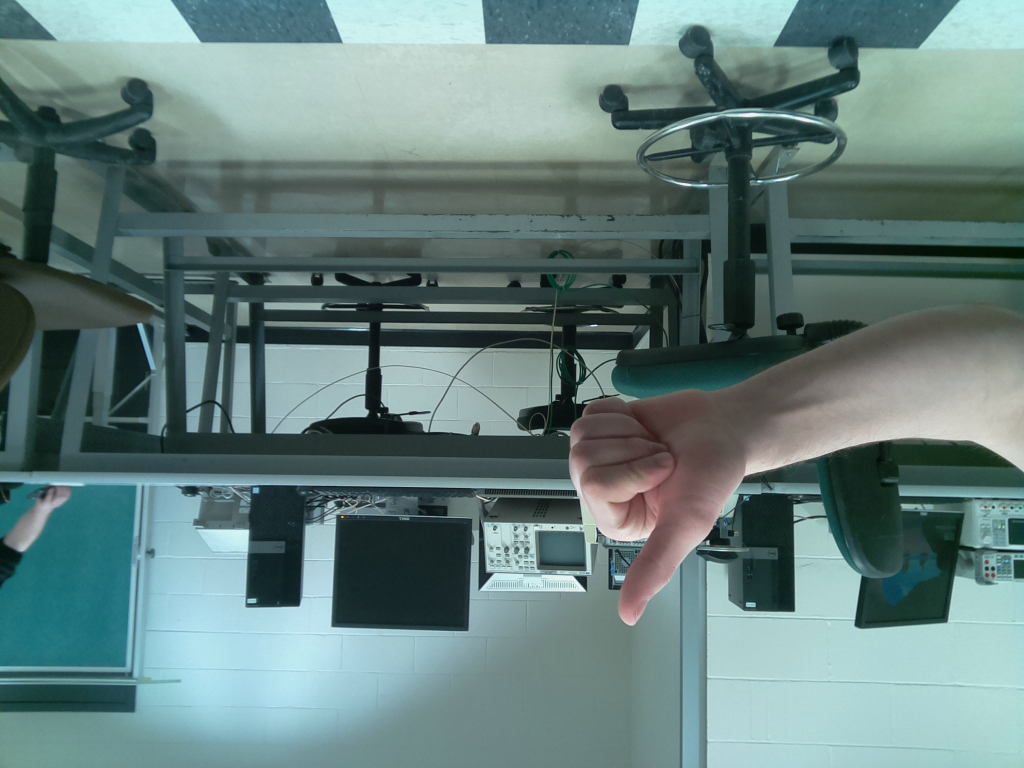
Calibration/image_51.png
