5sam/ScanUS/Calibration/Positions/92350335_556464058617746_7846651365685198848_n.png

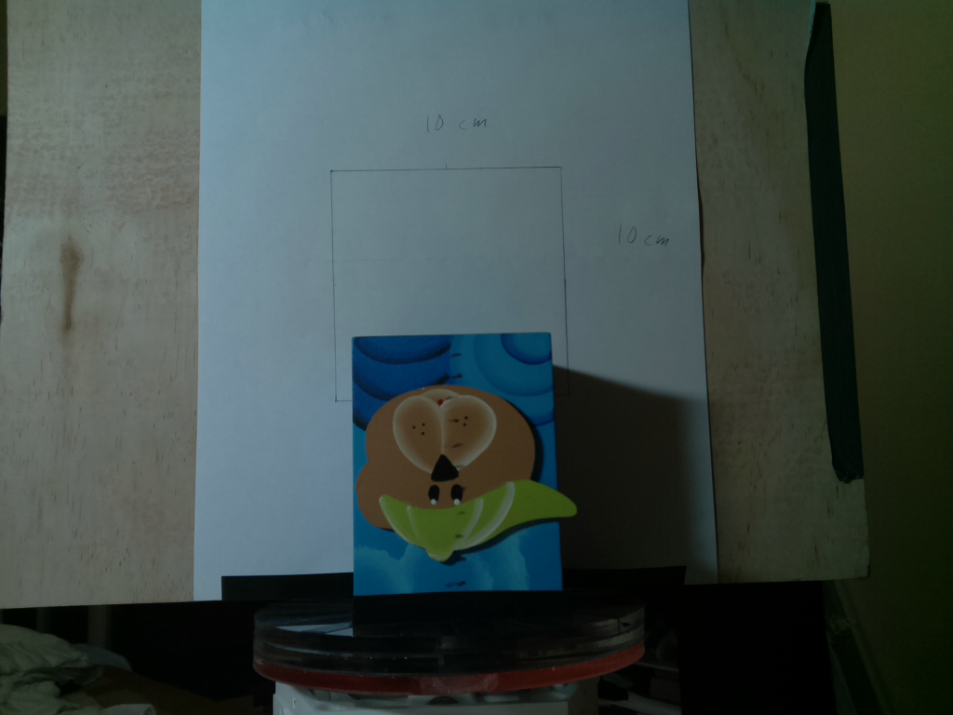
Calibration/Positions/92350335_556464058617746_7846651365685198848_n.png
