5sam/ScanUS/Calibration/Positions/92356242_684118695735569_870102718528618496_n.png

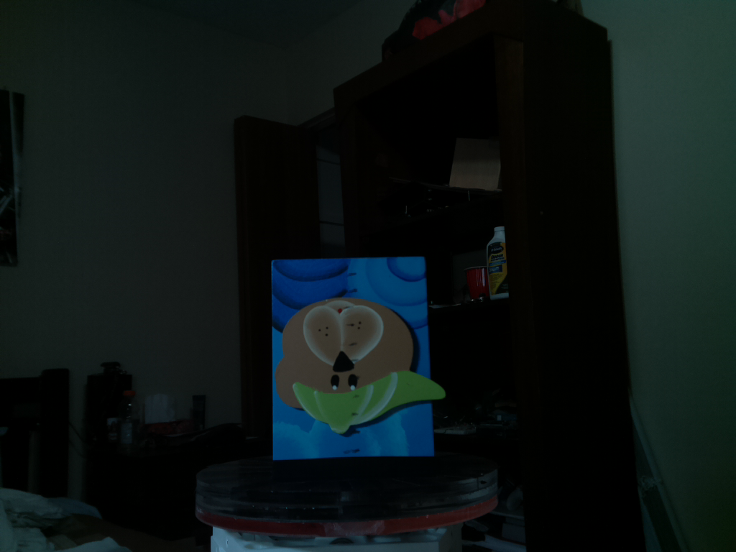
Calibration/Positions/92356242_684118695735569_870102718528618496_n.png
