5sam/ScanUS/Calibration/Positions/92400939_675701339671843_4756966280806793216_n.png

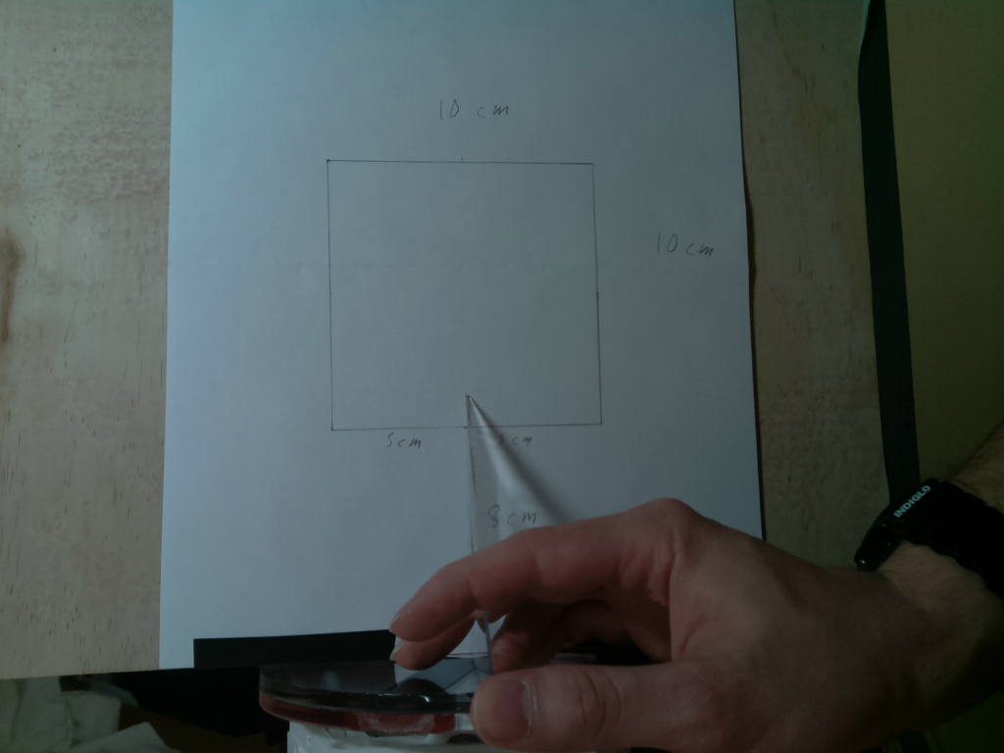
Calibration/Positions/92400939_675701339671843_4756966280806793216_n.png
