5sam/ScanUS/Calibration/removed_images/image_10.png

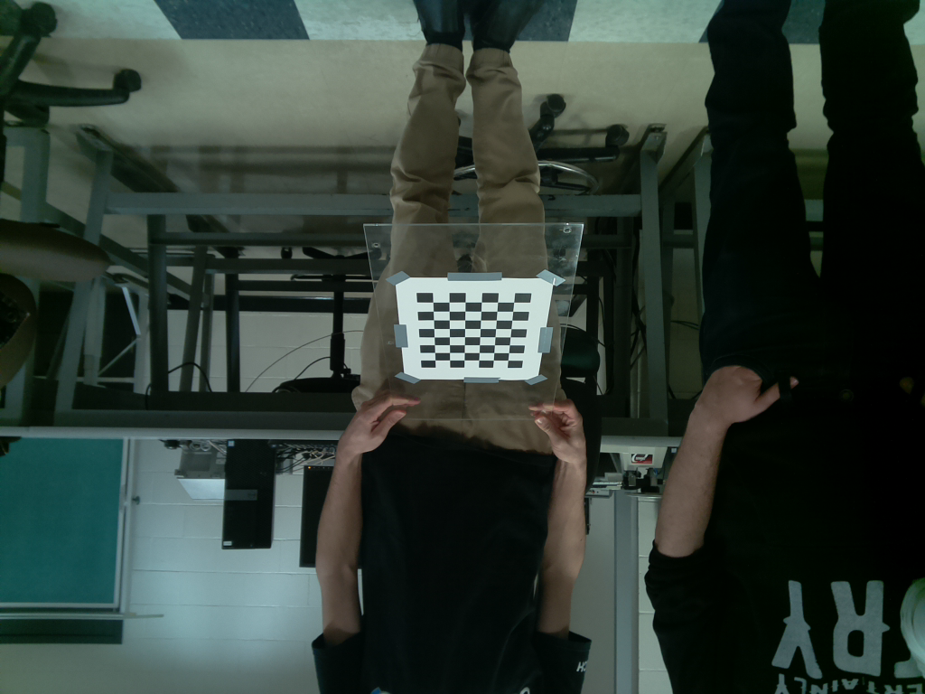
Calibration/removed_images/image_10.png
