5sam/ScanUS/Calibration/removed_images/image_18.png

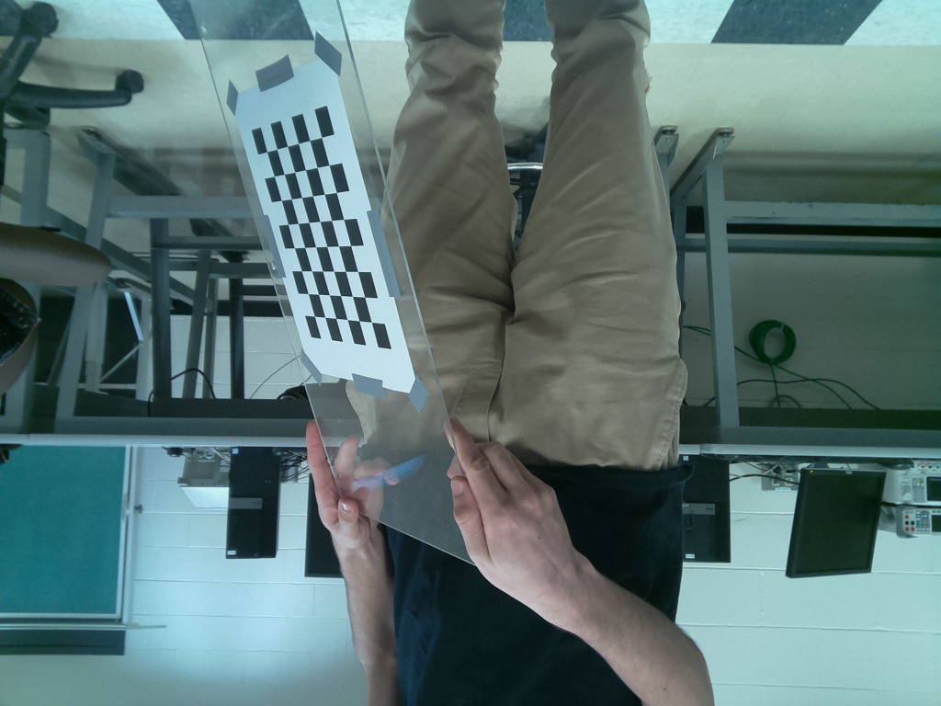
Calibration/removed_images/image_18.png
