5sam/ScanUS/Calibration/removed_images/image_22.png

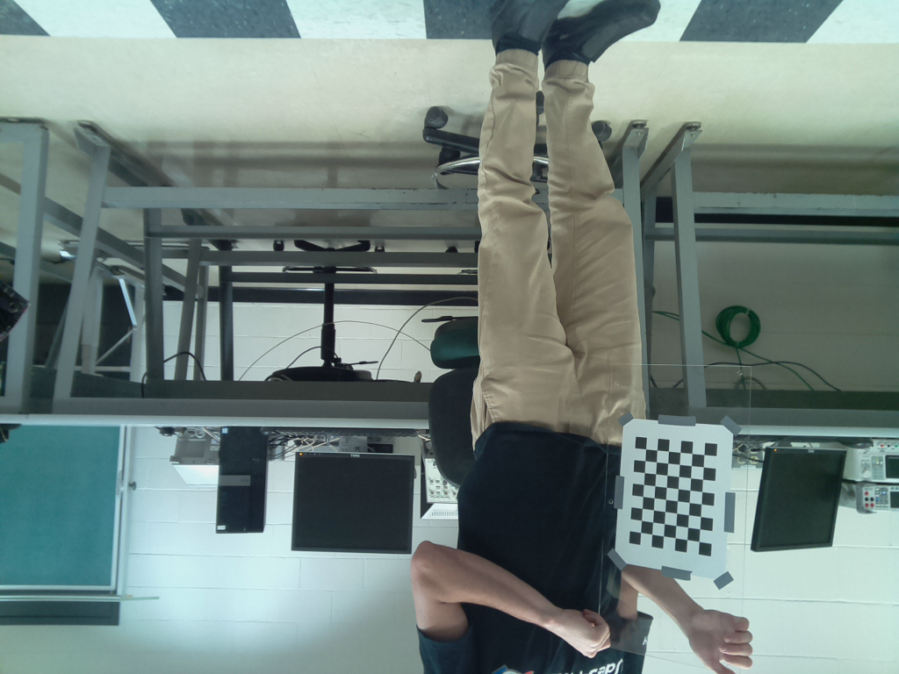
Calibration/removed_images/image_22.png
