5sam/ScanUS/Calibration/removed_images/image_37.png

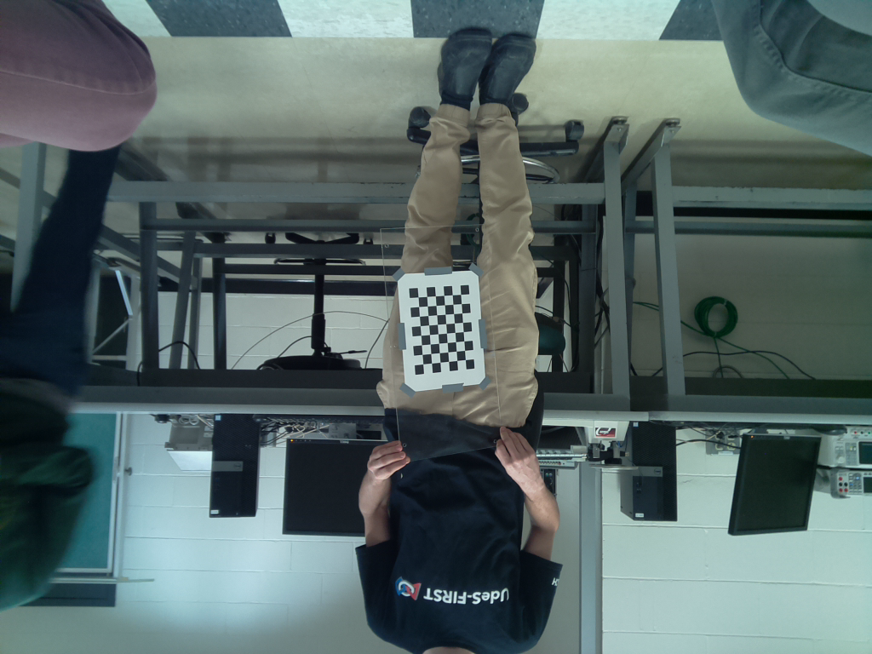
Calibration/removed_images/image_37.png
