5sam/ScanUS/Calibration/removed_images/image_38.png

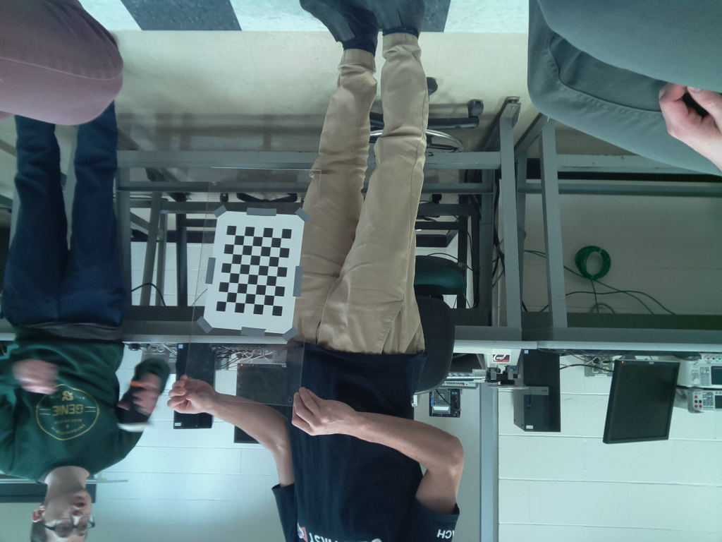
Calibration/removed_images/image_38.png
